fablabbcn/smartcitizen-kit-gases-pro-board/test_utils/data/source_A_board_1/source_W_board_1_lin_06.ods

Corriente | pedida | -1400 | - | corriente | leida_W | -1401.66 | 1.66 | pot0W_g | 3 | - | pot1W_f | 168
Corriente | pedida | -1399 | - | corriente | leida_W | -1400.64 | 1.64 | pot0W_g | 3 | - | pot1W_f | 179
Corriente | pedida | -1398 | - | corriente | leida_W | -1399.59 | 1.59 | pot0W_g | 3 | - | pot1W_f | 190
Corriente | pedida | -1397 | - | corriente | leida_W | -1398.64 | 1.64 | pot0W_g | 3 | - | pot1W_f | 200
Corriente | pedida | -1396 | - | corriente | leida_W | -1397.77 | 1.77 | pot0W_g | 3 | - | pot1W_f | 209
Corriente | pedida | -1395 | - | corriente | leida_W | -1396.81 | 1.81 | pot0W_g | 3 | - | pot1W_f | 219
Corriente | pedida | -1394 | - | corriente | leida_W | -1395.77 | 1.77 | pot0W_g | 3 | - | pot1W_f | 230
Corriente | pedida | -1393 | - | corriente | leida_W | -1394.59 | 1.59 | pot0W_g | 3 | - | pot1W_f | 242
Corriente | pedida | -1392 | - | corriente | leida_W | -1393.44 | 1.44 | pot0W_g | 4 | - | pot1W_f | 87
Corriente | pedida | -1391 | - | corriente | leida_W | -1392.45 | 1.45 | pot0W_g | 4 | - | pot1W_f | 97
Corriente | pedida | -1390 | - | corriente | leida_W | -1391.5 | 1.5 | pot0W_g | 4 | - | pot1W_f | 107
Corriente | pedida | -1389 | - | corriente | leida_W | -1390.45 | 1.45 | pot0W_g | 4 | - | pot1W_f | 118
Corriente | pedida | -1388 | - | corriente | leida_W | -1389.52 | 1.52 | pot0W_g | 4 | - | pot1W_f | 128
Corriente | pedida | -1387 | - | corriente | leida_W | -1388.48 | 1.48 | pot0W_g | 4 | - | pot1W_f | 139
Corriente | pedida | -1386 | - | corriente | leida_W | -1387.5 | 1.5 | pot0W_g | 4 | - | pot1W_f | 149
Corriente | pedida | -1385 | - | corriente | leida_W | -1386.44 | 1.44 | pot0W_g | 4 | - | pot1W_f | 160
Corriente | pedida | -1384 | - | corriente | leida_W | -1385.48 | 1.48 | pot0W_g | 4 | - | pot1W_f | 170
Corriente | pedida | -1383 | - | corriente | leida_W | -1384.53 | 1.53 | pot0W_g | 4 | - | pot1W_f | 180
Corriente | pedida | -1382 | - | corriente | leida_W | -1383.48 | 1.48 | pot0W_g | 4 | - | pot1W_f | 191
Corriente | pedida | -1381 | - | corriente | leida_W | -1382.52 | 1.52 | pot0W_g | 4 | - | pot1W_f | 201
Corriente | pedida | -1380 | - | corriente | leida_W | -1381.47 | 1.47 | pot0W_g | 4 | - | pot1W_f | 212
Corriente | pedida | -1379 | - | corriente | leida_W | -1380.48 | 1.48 | pot0W_g | 4 | - | pot1W_f | 222
Corriente | pedida | -1378 | - | corriente | leida_W | -1379.45 | 1.45 | pot0W_g | 4 | - | pot1W_f | 233
Corriente | pedida | -1377 | - | corriente | leida_W | -1378.48 | 1.48 | pot0W_g | 4 | - | pot1W_f | 243
Corriente | pedida | -1376 | - | corriente | leida_W | -1377.48 | 1.48 | pot0W_g | 5 | - | pot1W_f | 82
Corriente | pedida | -1375 | - | corriente | leida_W | -1376.55 | 1.55 | pot0W_g | 5 | - | pot1W_f | 92
Corriente | pedida | -1374 | - | corriente | leida_W | -1375.5 | 1.5 | pot0W_g | 5 | - | pot1W_f | 103
Corriente | pedida | -1373 | - | corriente | leida_W | -1374.56 | 1.56 | pot0W_g | 5 | - | pot1W_f | 113
Corriente | pedida | -1372 | - | corriente | leida_W | -1373.48 | 1.48 | pot0W_g | 5 | - | pot1W_f | 124
Corriente | pedida | -1371 | - | corriente | leida_W | -1372.44 | 1.44 | pot0W_g | 5 | - | pot1W_f | 135
Corriente | pedida | -1370 | - | corriente | leida_W | -1371.5 | 1.5 | pot0W_g | 5 | - | pot1W_f | 145
Corriente | pedida | -1369 | - | corriente | leida_W | -1370.42 | 1.42 | pot0W_g | 5 | - | pot1W_f | 156
Corriente | pedida | -1368 | - | corriente | leida_W | -1369.5 | 1.5 | pot0W_g | 5 | - | pot1W_f | 166
Corriente | pedida | -1367 | - | corriente | leida_W | -1368.44 | 1.44 | pot0W_g | 5 | - | pot1W_f | 177
Corriente | pedida | -1366 | - | corriente | leida_W | -1367.39 | 1.39 | pot0W_g | 5 | - | pot1W_f | 188
Corriente | pedida | -1365 | - | corriente | leida_W | -1366.42 | 1.42 | pot0W_g | 5 | - | pot1W_f | 198
Corriente | pedida | -1364 | - | corriente | leida_W | -1365.45 | 1.45 | pot0W_g | 5 | - | pot1W_f | 208
Corriente | pedida | -1363 | - | corriente | leida_W | -1364.45 | 1.45 | pot0W_g | 5 | - | pot1W_f | 219
Corriente | pedida | -1362 | - | corriente | leida_W | -1363.48 | 1.48 | pot0W_g | 5 | - | pot1W_f | 229
Corriente | pedida | -1361 | - | corriente | leida_W | -1362.39 | 1.39 | pot0W_g | 5 | - | pot1W_f | 240
Corriente | pedida | -1360 | - | corriente | leida_W | -1361.39 | 1.39 | pot0W_g | 6 | - | pot1W_f | 86
Corriente | pedida | -1359 | - | corriente | leida_W | -1360.44 | 1.44 | pot0W_g | 6 | - | pot1W_f | 96
Corriente | pedida | -1358 | - | corriente | leida_W | -1359.47 | 1.47 | pot0W_g | 6 | - | pot1W_f | 106
Corriente | pedida | -1357 | - | corriente | leida_W | -1358.42 | 1.42 | pot0W_g | 6 | - | pot1W_f | 117
Corriente | pedida | -1356 | - | corriente | leida_W | -1357.38 | 1.38 | pot0W_g | 6 | - | pot1W_f | 128
Corriente | pedida | -1355 | - | corriente | leida_W | -1356.45 | 1.45 | pot0W_g | 6 | - | pot1W_f | 138
Corriente | pedida | -1354 | - | corriente | leida_W | -1355.47 | 1.47 | pot0W_g | 6 | - | pot1W_f | 148
Corriente | pedida | -1353 | - | corriente | leida_W | -1354.41 | 1.41 | pot0W_g | 6 | - | pot1W_f | 159
Corriente | pedida | -1352 | - | corriente | leida_W | -1353.44 | 1.44 | pot0W_g | 6 | - | pot1W_f | 169
Corriente | pedida | -1351 | - | corriente | leida_W | -1352.41 | 1.41 | pot0W_g | 6 | - | pot1W_f | 180
Corriente | pedida | -1350 | - | corriente | leida_W | -1351.47 | 1.47 | pot0W_g | 6 | - | pot1W_f | 190
Corriente | pedida | -1349 | - | corriente | leida_W | -1350.39 | 1.39 | pot0W_g | 6 | - | pot1W_f | 201
Corriente | pedida | -1348 | - | corriente | leida_W | -1349.45 | 1.45 | pot0W_g | 6 | - | pot1W_f | 211
Corriente | pedida | -1347 | - | corriente | leida_W | -1348.39 | 1.39 | pot0W_g | 6 | - | pot1W_f | 222
Corriente | pedida | -1346 | - | corriente | leida_W | -1347.41 | 1.41 | pot0W_g | 6 | - | pot1W_f | 232
Corriente | pedida | -1345 | - | corriente | leida_W | -1346.47 | 1.47 | pot0W_g | 6 | - | pot1W_f | 242
Corriente | pedida | -1344 | - | corriente | leida_W | -1345.38 | 1.38 | pot0W_g | 7 | - | pot1W_f | 90
Corriente | pedida | -1343 | - | corriente | leida_W | -1344.39 | 1.39 | pot0W_g | 7 | - | pot1W_f | 100
Corriente | pedida | -1342 | - | corriente | leida_W | -1343.34 | 1.34 | pot0W_g | 7 | - | pot1W_f | 111
Corriente | pedida | -1341 | - | corriente | leida_W | -1342.39 | 1.39 | pot0W_g | 7 | - | pot1W_f | 121
Corriente | pedida | -1340 | - | corriente | leida_W | -1341.34 | 1.34 | pot0W_g | 7 | - | pot1W_f | 132
Corriente | pedida | -1339 | - | corriente | leida_W | -1340.41 | 1.41 | pot0W_g | 7 | - | pot1W_f | 142
Corriente | pedida | -1338 | - | corriente | leida_W | -1339.33 | 1.33 | pot0W_g | 7 | - | pot1W_f | 153
Corriente | pedida | -1337 | - | corriente | leida_W | -1338.38 | 1.38 | pot0W_g | 7 | - | pot1W_f | 163
Corriente | pedida | -1336 | - | corriente | leida_W | -1337.33 | 1.33 | pot0W_g | 7 | - | pot1W_f | 174
Corriente | pedida | -1335 | - | corriente | leida_W | -1336.31 | 1.31 | pot0W_g | 7 | - | pot1W_f | 185
Corriente | pedida | -1334 | - | corriente | leida_W | -1335.34 | 1.34 | pot0W_g | 7 | - | pot1W_f | 195
Corriente | pedida | -1333 | - | corriente | leida_W | -1334.31 | 1.31 | pot0W_g | 7 | - | pot1W_f | 206
Corriente | pedida | -1332 | - | corriente | leida_W | -1333.33 | 1.33 | pot0W_g | 7 | - | pot1W_f | 216
Corriente | pedida | -1331 | - | corriente | leida_W | -1332.27 | 1.27 | pot0W_g | 7 | - | pot1W_f | 227
Corriente | pedida | -1330 | - | corriente | leida_W | -1331.3 | 1.3 | pot0W_g | 7 | - | pot1W_f | 237
Corriente | pedida | -1329 | - | corriente | leida_W | -1330.23 | 1.23 | pot0W_g | 7 | - | pot1W_f | 248
Corriente | pedida | -1328 | - | corriente | leida_W | -1329.3 | 1.3 | pot0W_g | 8 | - | pot1W_f | 114
Corriente | pedida | -1327 | - | corriente | leida_W | -1328.38 | 1.38 | pot0W_g | 8 | - | pot1W_f | 124
Corriente | pedida | -1326 | - | corriente | leida_W | -1327.28 | 1.28 | pot0W_g | 8 | - | pot1W_f | 135
Corriente | pedida | -1325 | - | corriente | leida_W | -1326.25 | 1.25 | pot0W_g | 8 | - | pot1W_f | 146
Corriente | pedida | -1324 | - | corriente | leida_W | -1325.3 | 1.3 | pot0W_g | 8 | - | pot1W_f | 156
Corriente | pedida | -1323 | - | corriente | leida_W | -1324.33 | 1.33 | pot0W_g | 8 | - | pot1W_f | 166
Corriente | pedida | -1322 | - | corriente | leida_W | -1323.3 | 1.3 | pot0W_g | 8 | - | pot1W_f | 177
Corriente | pedida | -1321 | - | corriente | leida_W | -1322.27 | 1.27 | pot0W_g | 8 | - | pot1W_f | 188
Corriente | pedida | -1320 | - | corriente | leida_W | -1321.3 | 1.3 | pot0W_g | 8 | - | pot1W_f | 198
Corriente | pedida | -1319 | - | corriente | leida_W | -1320.22 | 1.22 | pot0W_g | 8 | - | pot1W_f | 209
Corriente | pedida | -1318 | - | corriente | leida_W | -1319.28 | 1.28 | pot0W_g | 8 | - | pot1W_f | 219
Corriente | pedida | -1317 | - | corriente | leida_W | -1318.31 | 1.31 | pot0W_g | 8 | - | pot1W_f | 229
Corriente | pedida | -1316 | - | corriente | leida_W | -1317.25 | 1.25 | pot0W_g | 8 | - | pot1W_f | 240
Corriente | pedida | -1315 | - | corriente | leida_W | -1316.25 | 1.25 | pot0W_g | 9 | - | pot1W_f | 91
Corriente | pedida | -1314 | - | corriente | leida_W | -1315.3 | 1.3 | pot0W_g | 9 | - | pot1W_f | 101
Corriente | pedida | -1313 | - | corriente | leida_W | -1314.36 | 1.36 | pot0W_g | 9 | - | pot1W_f | 111
Corriente | pedida | -1312 | - | corriente | leida_W | -1313.3 | 1.3 | pot0W_g | 9 | - | pot1W_f | 122
Corriente | pedida | -1311 | - | corriente | leida_W | -1312.33 | 1.33 | pot0W_g | 9 | - | pot1W_f | 132
Corriente | pedida | -1310 | - | corriente | leida_W | -1311.31 | 1.31 | pot0W_g | 9 | - | pot1W_f | 143
Corriente | pedida | -1309 | - | corriente | leida_W | -1310.33 | 1.33 | pot0W_g | 9 | - | pot1W_f | 153
Corriente | pedida | -1308 | - | corriente | leida_W | -1309.28 | 1.28 | pot0W_g | 9 | - | pot1W_f | 164
Corriente | pedida | -1307 | - | corriente | leida_W | -1308.33 | 1.33 | pot0W_g | 9 | - | pot1W_f | 174
Corriente | pedida | -1306 | - | corriente | leida_W | -1307.28 | 1.28 | pot0W_g | 9 | - | pot1W_f | 185
Corriente | pedida | -1305 | - | corriente | leida_W | -1306.33 | 1.33 | pot0W_g | 9 | - | pot1W_f | 195
Corriente | pedida | -1304 | - | corriente | leida_W | -1305.27 | 1.27 | pot0W_g | 9 | - | pot1W_f | 206
Corriente | pedida | -1303 | - | corriente | leida_W | -1304.33 | 1.33 | pot0W_g | 9 | - | pot1W_f | 216
Corriente | pedida | -1302 | - | corriente | leida_W | -1303.27 | 1.27 | pot0W_g | 9 | - | pot1W_f | 227
Corriente | pedida | -1301 | - | corriente | leida_W | -1302.31 | 1.31 | pot0W_g | 9 | - | pot1W_f | 237
Corriente | pedida | -1300 | - | corriente | leida_W | -1301.33 | 1.33 | pot0W_g | 9 | - | pot1W_f | 247
Corriente | pedida | -1299 | - | corriente | leida_W | -1300.22 | 1.22 | pot0W_g | 10 | - | pot1W_f | 98
Corriente | pedida | -1298 | - | corriente | leida_W | -1299.28 | 1.28 | pot0W_g | 10 | - | pot1W_f | 108
Corriente | pedida | -1297 | - | corriente | leida_W | -1298.34 | 1.34 | pot0W_g | 10 | - | pot1W_f | 118
Corriente | pedida | -1296 | - | corriente | leida_W | -1297.3 | 1.3 | pot0W_g | 10 | - | pot1W_f | 129
Corriente | pedida | -1295 | - | corriente | leida_W | -1296.34 | 1.34 | pot0W_g | 10 | - | pot1W_f | 139
Corriente | pedida | -1294 | - | corriente | leida_W | -1295.3 | 1.3 | pot0W_g | 10 | - | pot1W_f | 150
Corriente | pedida | -1293 | - | corriente | leida_W | -1294.31 | 1.31 | pot0W_g | 10 | - | pot1W_f | 160
Corriente | pedida | -1292 | - | corriente | leida_W | -1293.28 | 1.28 | pot0W_g | 10 | - | pot1W_f | 171
Corriente | pedida | -1291 | - | corriente | leida_W | -1292.34 | 1.34 | pot0W_g | 10 | - | pot1W_f | 181
Corriente | pedida | -1290 | - | corriente | leida_W | -1291.38 | 1.38 | pot0W_g | 10 | - | pot1W_f | 191
Corriente | pedida | -1289 | - | corriente | leida_W | -1290.31 | 1.31 | pot0W_g | 10 | - | pot1W_f | 202
Corriente | pedida | -1288 | - | corriente | leida_W | -1289.38 | 1.38 | pot0W_g | 10 | - | pot1W_f | 212
Corriente | pedida | -1287 | - | corriente | leida_W | -1288.3 | 1.3 | pot0W_g | 10 | - | pot1W_f | 223
Corriente | pedida | -1286 | - | corriente | leida_W | -1287.34 | 1.34 | pot0W_g | 10 | - | pot1W_f | 233
Corriente | pedida | -1285 | - | corriente | leida_W | -1286.3 | 1.3 | pot0W_g | 10 | - | pot1W_f | 244
Corriente | pedida | -1284 | - | corriente | leida_W | -1285.25 | 1.25 | pot0W_g | 11 | - | pot1W_f | 100
Corriente | pedida | -1283 | - | corriente | leida_W | -1284.27 | 1.27 | pot0W_g | 11 | - | pot1W_f | 110
Corriente | pedida | -1282 | - | corriente | leida_W | -1283.31 | 1.31 | pot0W_g | 11 | - | pot1W_f | 120
Corriente | pedida | -1281 | - | corriente | leida_W | -1282.27 | 1.27 | pot0W_g | 11 | - | pot1W_f | 131
Corriente | pedida | -1280 | - | corriente | leida_W | -1281.33 | 1.33 | pot0W_g | 11 | - | pot1W_f | 141
Corriente | pedida | -1279 | - | corriente | leida_W | -1280.27 | 1.27 | pot0W_g | 11 | - | pot1W_f | 152
Corriente | pedida | -1278 | - | corriente | leida_W | -1279.23 | 1.23 | pot0W_g | 11 | - | pot1W_f | 163
Corriente | pedida | -1277 | - | corriente | leida_W | -1278.25 | 1.25 | pot0W_g | 11 | - | pot1W_f | 173
Corriente | pedida | -1276 | - | corriente | leida_W | -1277.19 | 1.19 | pot0W_g | 11 | - | pot1W_f | 184
Corriente | pedida | -1275 | - | corriente | leida_W | -1276.28 | 1.28 | pot0W_g | 11 | - | pot1W_f | 194
Corriente | pedida | -1274 | - | corriente | leida_W | -1275.2 | 1.2 | pot0W_g | 11 | - | pot1W_f | 205
Corriente | pedida | -1273 | - | corriente | leida_W | -1274.27 | 1.27 | pot0W_g | 11 | - | pot1W_f | 215
Corriente | pedida | -1272 | - | corriente | leida_W | -1273.19 | 1.19 | pot0W_g | 11 | - | pot1W_f | 226
Corriente | pedida | -1271 | - | corriente | leida_W | -1272.23 | 1.23 | pot0W_g | 11 | - | pot1W_f | 236
Corriente | pedida | -1270 | - | corriente | leida_W | -1271.17 | 1.17 | pot0W_g | 11 | - | pot1W_f | 247
Corriente | pedida | -1269 | - | corriente | leida_W | -1270.16 | 1.16 | pot0W_g | 12 | - | pot1W_f | 102
Corriente | pedida | -1268 | - | corriente | leida_W | -1269.2 | 1.2 | pot0W_g | 12 | - | pot1W_f | 112
Corriente | pedida | -1267 | - | corriente | leida_W | -1268.14 | 1.14 | pot0W_g | 12 | - | pot1W_f | 123
Corriente | pedida | -1266 | - | corriente | leida_W | -1267.19 | 1.19 | pot0W_g | 12 | - | pot1W_f | 133
Corriente | pedida | -1265 | - | corriente | leida_W | -1266.14 | 1.14 | pot0W_g | 12 | - | pot1W_f | 144
Corriente | pedida | -1264 | - | corriente | leida_W | -1265.17 | 1.17 | pot0W_g | 12 | - | pot1W_f | 154
Corriente | pedida | -1263 | - | corriente | leida_W | -1264.2 | 1.2 | pot0W_g | 12 | - | pot1W_f | 164
Corriente | pedida | -1262 | - | corriente | leida_W | -1263.17 | 1.17 | pot0W_g | 12 | - | pot1W_f | 175
Corriente | pedida | -1261 | - | corriente | leida_W | -1262.11 | 1.11 | pot0W_g | 12 | - | pot1W_f | 186
Corriente | pedida | -1260 | - | corriente | leida_W | -1261.14 | 1.14 | pot0W_g | 12 | - | pot1W_f | 196
Corriente | pedida | -1259 | - | corriente | leida_W | -1260.08 | 1.08 | pot0W_g | 12 | - | pot1W_f | 207
Corriente | pedida | -1258 | - | corriente | leida_W | -1259.13 | 1.13 | pot0W_g | 12 | - | pot1W_f | 217
Corriente | pedida | -1257 | - | corriente | leida_W | -1258.06 | 1.06 | pot0W_g | 12 | - | pot1W_f | 228
Corriente | pedida | -1256 | - | corriente | leida_W | -1257.11 | 1.11 | pot0W_g | 12 | - | pot1W_f | 238
Corriente | pedida | -1255 | - | corriente | leida_W | -1256.11 | 1.11 | pot0W_g | 12 | - | pot1W_f | 248
Corriente | pedida | -1254 | - | corriente | leida_W | -1255.13 | 1.13 | pot0W_g | 13 | - | pot1W_f | 99
Corriente | pedida | -1253 | - | corriente | leida_W | -1254.11 | 1.11 | pot0W_g | 13 | - | pot1W_f | 110
Corriente | pedida | -1252 | - | corriente | leida_W | -1253.14 | 1.14 | pot0W_g | 13 | - | pot1W_f | 120
Corriente | pedida | -1251 | - | corriente | leida_W | -1252.09 | 1.09 | pot0W_g | 13 | - | pot1W_f | 131
Corriente | pedida | -1250 | - | corriente | leida_W | -1251.14 | 1.14 | pot0W_g | 13 | - | pot1W_f | 141
Corriente | pedida | -1249 | - | corriente | leida_W | -1250.19 | 1.19 | pot0W_g | 13 | - | pot1W_f | 151
Corriente | pedida | -1248 | - | corriente | leida_W | -1249.13 | 1.13 | pot0W_g | 13 | - | pot1W_f | 162
Corriente | pedida | -1247 | - | corriente | leida_W | -1248.08 | 1.08 | pot0W_g | 13 | - | pot1W_f | 173
Corriente | pedida | -1246 | - | corriente | leida_W | -1247.14 | 1.14 | pot0W_g | 13 | - | pot1W_f | 183
Corriente | pedida | -1245 | - | corriente | leida_W | -1246.08 | 1.08 | pot0W_g | 13 | - | pot1W_f | 194
Corriente | pedida | -1244 | - | corriente | leida_W | -1245.13 | 1.13 | pot0W_g | 13 | - | pot1W_f | 204
Corriente | pedida | -1243 | - | corriente | leida_W | -1244.16 | 1.16 | pot0W_g | 13 | - | pot1W_f | 214
Corriente | pedida | -1242 | - | corriente | leida_W | -1243.11 | 1.11 | pot0W_g | 13 | - | pot1W_f | 225
Corriente | pedida | -1241 | - | corriente | leida_W | -1242.13 | 1.13 | pot0W_g | 13 | - | pot1W_f | 235
Corriente | pedida | -1240 | - | corriente | leida_W | -1241.08 | 1.08 | pot0W_g | 13 | - | pot1W_f | 246
Corriente | pedida | -1239 | - | corriente | leida_W | -1240.06 | 1.06 | pot0W_g | 14 | - | pot1W_f | 103
Corriente | pedida | -1238 | - | corriente | leida_W | -1239.11 | 1.11 | pot0W_g | 14 | - | pot1W_f | 113
Corriente | pedida | -1237 | - | corriente | leida_W | -1238.05 | 1.05 | pot0W_g | 14 | - | pot1W_f | 124
Corriente | pedida | -1236 | - | corriente | leida_W | -1237.11 | 1.11 | pot0W_g | 14 | - | pot1W_f | 134
Corriente | pedida | -1235 | - | corriente | leida_W | -1236.05 | 1.05 | pot0W_g | 14 | - | pot1W_f | 145
Corriente | pedida | -1234 | - | corriente | leida_W | -1235.09 | 1.09 | pot0W_g | 14 | - | pot1W_f | 155
Corriente | pedida | -1233 | - | corriente | leida_W | -1234.14 | 1.14 | pot0W_g | 14 | - | pot1W_f | 165
Corriente | pedida | -1232 | - | corriente | leida_W | -1233.09 | 1.09 | pot0W_g | 14 | - | pot1W_f | 176
Corriente | pedida | -1231 | - | corriente | leida_W | -1232.02 | 1.02 | pot0W_g | 14 | - | pot1W_f | 187
Corriente | pedida | -1230 | - | corriente | leida_W | -1231.06 | 1.06 | pot0W_g | 14 | - | pot1W_f | 197
Corriente | pedida | -1229 | - | corriente | leida_W | -1230.11 | 1.11 | pot0W_g | 14 | - | pot1W_f | 207
Corriente | pedida | -1228 | - | corriente | leida_W | -1229.06 | 1.06 | pot0W_g | 14 | - | pot1W_f | 218
Corriente | pedida | -1227 | - | corriente | leida_W | -1228.09 | 1.09 | pot0W_g | 14 | - | pot1W_f | 228
Corriente | pedida | -1226 | - | corriente | leida_W | -1227.06 | 1.06 | pot0W_g | 14 | - | pot1W_f | 239
Corriente | pedida | -1225 | - | corriente | leida_W | -1226.09 | 1.09 | pot0W_g | 14 | - | pot1W_f | 249
Corriente | pedida | -1224 | - | corriente | leida_W | -1225.09 | 1.09 | pot0W_g | 15 | - | pot1W_f | 107
Corriente | pedida | -1223 | - | corriente | leida_W | -1224.13 | 1.13 | pot0W_g | 15 | - | pot1W_f | 117
Corriente | pedida | -1222 | - | corriente | leida_W | -1223.08 | 1.08 | pot0W_g | 15 | - | pot1W_f | 128
Corriente | pedida | -1221 | - | corriente | leida_W | -1222.11 | 1.11 | pot0W_g | 15 | - | pot1W_f | 138
Corriente | pedida | -1220 | - | corriente | leida_W | -1221.09 | 1.09 | pot0W_g | 15 | - | pot1W_f | 149
Corriente | pedida | -1219 | - | corriente | leida_W | -1220.02 | 1.02 | pot0W_g | 15 | - | pot1W_f | 160
Corriente | pedida | -1218 | - | corriente | leida_W | -1219.09 | 1.09 | pot0W_g | 15 | - | pot1W_f | 170
Corriente | pedida | -1217 | - | corriente | leida_W | -1218.13 | 1.13 | pot0W_g | 15 | - | pot1W_f | 180
Corriente | pedida | -1216 | - | corriente | leida_W | -1217.06 | 1.06 | pot0W_g | 15 | - | pot1W_f | 191
Corriente | pedida | -1215 | - | corriente | leida_W | -1216.13 | 1.13 | pot0W_g | 15 | - | pot1W_f | 201
Corriente | pedida | -1214 | - | corriente | leida_W | -1215.06 | 1.06 | pot0W_g | 15 | - | pot1W_f | 212
Corriente | pedida | -1213 | - | corriente | leida_W | -1214.13 | 1.13 | pot0W_g | 15 | - | pot1W_f | 222
Corriente | pedida | -1212 | - | corriente | leida_W | -1213.06 | 1.06 | pot0W_g | 15 | - | pot1W_f | 233
Corriente | pedida | -1211 | - | corriente | leida_W | -1212.09 | 1.09 | pot0W_g | 15 | - | pot1W_f | 243
Corriente | pedida | -1210 | - | corriente | leida_W | -1211.13 | 1.13 | pot0W_g | 16 | - | pot1W_f | 91
Corriente | pedida | -1209 | - | corriente | leida_W | -1210.16 | 1.16 | pot0W_g | 16 | - | pot1W_f | 101
Corriente | pedida | -1208 | - | corriente | leida_W | -1209.09 | 1.09 | pot0W_g | 16 | - | pot1W_f | 112
Corriente | pedida | -1207 | - | corriente | leida_W | -1208.14 | 1.14 | pot0W_g | 16 | - | pot1W_f | 122
Corriente | pedida | -1206 | - | corriente | leida_W | -1207.11 | 1.11 | pot0W_g | 16 | - | pot1W_f | 133
Corriente | pedida | -1205 | - | corriente | leida_W | -1206.14 | 1.14 | pot0W_g | 16 | - | pot1W_f | 143
Corriente | pedida | -1204 | - | corriente | leida_W | -1205.09 | 1.09 | pot0W_g | 16 | - | pot1W_f | 154
Corriente | pedida | -1203 | - | corriente | leida_W | -1204.16 | 1.16 | pot0W_g | 16 | - | pot1W_f | 164
Corriente | pedida | -1202 | - | corriente | leida_W | -1203.09 | 1.09 | pot0W_g | 16 | - | pot1W_f | 175
Corriente | pedida | -1201 | - | corriente | leida_W | -1202.14 | 1.14 | pot0W_g | 16 | - | pot1W_f | 185
Corriente | pedida | -1200 | - | corriente | leida_W | -1201.19 | 1.19 | pot0W_g | 16 | - | pot1W_f | 195
Corriente | pedida | -1199 | - | corriente | leida_W | -1200.14 | 1.14 | pot0W_g | 16 | - | pot1W_f | 206
Corriente | pedida | -1198 | - | corriente | leida_W | -1199.19 | 1.19 | pot0W_g | 16 | - | pot1W_f | 216
Corriente | pedida | -1197 | - | corriente | leida_W | -1198.11 | 1.11 | pot0W_g | 16 | - | pot1W_f | 227
Corriente | pedida | -1196 | - | corriente | leida_W | -1197.17 | 1.17 | pot0W_g | 16 | - | pot1W_f | 237
Corriente | pedida | -1195 | - | corriente | leida_W | -1196.19 | 1.19 | pot0W_g | 16 | - | pot1W_f | 247
Corriente | pedida | -1194 | - | corriente | leida_W | -1195.19 | 1.19 | pot0W_g | 17 | - | pot1W_f | 109
Corriente | pedida | -1193 | - | corriente | leida_W | -1194.23 | 1.23 | pot0W_g | 17 | - | pot1W_f | 119
Corriente | pedida | -1192 | - | corriente | leida_W | -1193.16 | 1.16 | pot0W_g | 17 | - | pot1W_f | 130
Corriente | pedida | -1191 | - | corriente | leida_W | -1192.11 | 1.11 | pot0W_g | 17 | - | pot1W_f | 141
Corriente | pedida | -1190 | - | corriente | leida_W | -1191.14 | 1.14 | pot0W_g | 17 | - | pot1W_f | 151
Corriente | pedida | -1189 | - | corriente | leida_W | -1190.17 | 1.17 | pot0W_g | 17 | - | pot1W_f | 161
Corriente | pedida | -1188 | - | corriente | leida_W | -1189.11 | 1.11 | pot0W_g | 17 | - | pot1W_f | 172
Corriente | pedida | -1187 | - | corriente | leida_W | -1188.19 | 1.19 | pot0W_g | 17 | - | pot1W_f | 182
Corriente | pedida | -1186 | - | corriente | leida_W | -1187.14 | 1.14 | pot0W_g | 17 | - | pot1W_f | 193
Corriente | pedida | -1185 | - | corriente | leida_W | -1186.16 | 1.16 | pot0W_g | 17 | - | pot1W_f | 203
Corriente | pedida | -1184 | - | corriente | leida_W | -1185.09 | 1.09 | pot0W_g | 17 | - | pot1W_f | 214
Corriente | pedida | -1183 | - | corriente | leida_W | -1184.05 | 1.05 | pot0W_g | 17 | - | pot1W_f | 225
Corriente | pedida | -1182 | - | corriente | leida_W | -1183.17 | 1.17 | pot0W_g | 17 | - | pot1W_f | 234
Corriente | pedida | -1181 | - | corriente | leida_W | -1182.11 | 1.11 | pot0W_g | 17 | - | pot1W_f | 245
Corriente | pedida | -1180 | - | corriente | leida_W | -1181.06 | 1.06 | pot0W_g | 18 | - | pot1W_f | 106
Corriente | pedida | -1179 | - | corriente | leida_W | -1180.13 | 1.13 | pot0W_g | 18 | - | pot1W_f | 116
Corriente | pedida | -1178 | - | corriente | leida_W | -1179.16 | 1.16 | pot0W_g | 18 | - | pot1W_f | 126
Corriente | pedida | -1177 | - | corriente | leida_W | -1178.13 | 1.13 | pot0W_g | 18 | - | pot1W_f | 137
Corriente | pedida | -1176 | - | corriente | leida_W | -1177.08 | 1.08 | pot0W_g | 18 | - | pot1W_f | 148
Corriente | pedida | -1175 | - | corriente | leida_W | -1176.11 | 1.11 | pot0W_g | 18 | - | pot1W_f | 158
Corriente | pedida | -1174 | - | corriente | leida_W | -1175.16 | 1.16 | pot0W_g | 18 | - | pot1W_f | 168
Corriente | pedida | -1173 | - | corriente | leida_W | -1174.13 | 1.13 | pot0W_g | 18 | - | pot1W_f | 179
Corriente | pedida | -1172 | - | corriente | leida_W | -1173.17 | 1.17 | pot0W_g | 18 | - | pot1W_f | 189
Corriente | pedida | -1171 | - | corriente | leida_W | -1172.14 | 1.14 | pot0W_g | 18 | - | pot1W_f | 200
Corriente | pedida | -1170 | - | corriente | leida_W | -1171.14 | 1.14 | pot0W_g | 18 | - | pot1W_f | 210
Corriente | pedida | -1169 | - | corriente | leida_W | -1170.11 | 1.11 | pot0W_g | 18 | - | pot1W_f | 221
Corriente | pedida | -1168 | - | corriente | leida_W | -1169.14 | 1.14 | pot0W_g | 18 | - | pot1W_f | 231
Corriente | pedida | -1167 | - | corriente | leida_W | -1168.17 | 1.17 | pot0W_g | 18 | - | pot1W_f | 241
Corriente | pedida | -1166 | - | corriente | leida_W | -1167.06 | 1.06 | pot0W_g | 19 | - | pot1W_f | 108
Corriente | pedida | -1165 | - | corriente | leida_W | -1166.11 | 1.11 | pot0W_g | 19 | - | pot1W_f | 118
Corriente | pedida | -1164 | - | corriente | leida_W | -1165.13 | 1.13 | pot0W_g | 19 | - | pot1W_f | 128
Corriente | pedida | -1163 | - | corriente | leida_W | -1164.09 | 1.09 | pot0W_g | 19 | - | pot1W_f | 139
Corriente | pedida | -1162 | - | corriente | leida_W | -1163.13 | 1.13 | pot0W_g | 19 | - | pot1W_f | 149
Corriente | pedida | -1161 | - | corriente | leida_W | -1162.08 | 1.08 | pot0W_g | 19 | - | pot1W_f | 160
Corriente | pedida | -1160 | - | corriente | leida_W | -1161.13 | 1.13 | pot0W_g | 19 | - | pot1W_f | 170
Corriente | pedida | -1159 | - | corriente | leida_W | -1160.17 | 1.17 | pot0W_g | 19 | - | pot1W_f | 180
Corriente | pedida | -1158 | - | corriente | leida_W | -1159.14 | 1.14 | pot0W_g | 19 | - | pot1W_f | 191
Corriente | pedida | -1157 | - | corriente | leida_W | -1158.17 | 1.17 | pot0W_g | 19 | - | pot1W_f | 201
Corriente | pedida | -1156 | - | corriente | leida_W | -1157.16 | 1.16 | pot0W_g | 19 | - | pot1W_f | 212
Corriente | pedida | -1155 | - | corriente | leida_W | -1156.19 | 1.19 | pot0W_g | 19 | - | pot1W_f | 222
Corriente | pedida | -1154 | - | corriente | leida_W | -1155.22 | 1.22 | pot0W_g | 19 | - | pot1W_f | 232
Corriente | pedida | -1153 | - | corriente | leida_W | -1154.14 | 1.14 | pot0W_g | 19 | - | pot1W_f | 243
Corriente | pedida | -1152 | - | corriente | leida_W | -1153.06 | 1.06 | pot0W_g | 20 | - | pot1W_f | 109
Corriente | pedida | -1151 | - | corriente | leida_W | -1152.13 | 1.13 | pot0W_g | 20 | - | pot1W_f | 119
Corriente | pedida | -1150 | - | corriente | leida_W | -1151.16 | 1.16 | pot0W_g | 20 | - | pot1W_f | 129
Corriente | pedida | -1149 | - | corriente | leida_W | -1150.11 | 1.11 | pot0W_g | 20 | - | pot1W_f | 140
Corriente | pedida | -1148 | - | corriente | leida_W | -1149.16 | 1.16 | pot0W_g | 20 | - | pot1W_f | 150
Corriente | pedida | -1147 | - | corriente | leida_W | -1148.19 | 1.19 | pot0W_g | 20 | - | pot1W_f | 160
Corriente | pedida | -1146 | - | corriente | leida_W | -1147.23 | 1.23 | pot0W_g | 20 | - | pot1W_f | 170
Corriente | pedida | -1145 | - | corriente | leida_W | -1146.17 | 1.17 | pot0W_g | 20 | - | pot1W_f | 181
Corriente | pedida | -1144 | - | corriente | leida_W | -1145.14 | 1.14 | pot0W_g | 20 | - | pot1W_f | 192
Corriente | pedida | -1143 | - | corriente | leida_W | -1144.3 | 1.3 | pot0W_g | 20 | - | pot1W_f | 201
Corriente | pedida | -1142 | - | corriente | leida_W | -1143.22 | 1.22 | pot0W_g | 20 | - | pot1W_f | 212
Corriente | pedida | -1141 | - | corriente | leida_W | -1142.28 | 1.28 | pot0W_g | 20 | - | pot1W_f | 222
Corriente | pedida | -1140 | - | corriente | leida_W | -1141.22 | 1.22 | pot0W_g | 20 | - | pot1W_f | 233
Corriente | pedida | -1139 | - | corriente | leida_W | -1140.23 | 1.23 | pot0W_g | 20 | - | pot1W_f | 243
Corriente | pedida | -1138 | - | corriente | leida_W | -1139.19 | 1.19 | pot0W_g | 21 | - | pot1W_f | 105
Corriente | pedida | -1137 | - | corriente | leida_W | -1138.23 | 1.23 | pot0W_g | 21 | - | pot1W_f | 115
Corriente | pedida | -1136 | - | corriente | leida_W | -1137.28 | 1.28 | pot0W_g | 21 | - | pot1W_f | 125
Corriente | pedida | -1135 | - | corriente | leida_W | -1136.22 | 1.22 | pot0W_g | 21 | - | pot1W_f | 136
Corriente | pedida | -1134 | - | corriente | leida_W | -1135.27 | 1.27 | pot0W_g | 21 | - | pot1W_f | 146
Corriente | pedida | -1133 | - | corriente | leida_W | -1134.22 | 1.22 | pot0W_g | 21 | - | pot1W_f | 157
Corriente | pedida | -1132 | - | corriente | leida_W | -1133.27 | 1.27 | pot0W_g | 21 | - | pot1W_f | 167
Corriente | pedida | -1131 | - | corriente | leida_W | -1132.33 | 1.33 | pot0W_g | 21 | - | pot1W_f | 177
Corriente | pedida | -1130 | - | corriente | leida_W | -1131.27 | 1.27 | pot0W_g | 21 | - | pot1W_f | 188
Corriente | pedida | -1129 | - | corriente | leida_W | -1130.3 | 1.3 | pot0W_g | 21 | - | pot1W_f | 198
Corriente | pedida | -1128 | - | corriente | leida_W | -1129.27 | 1.27 | pot0W_g | 21 | - | pot1W_f | 209
Corriente | pedida | -1127 | - | corriente | leida_W | -1128.3 | 1.3 | pot0W_g | 21 | - | pot1W_f | 219
Corriente | pedida | -1126 | - | corriente | leida_W | -1127.34 | 1.34 | pot0W_g | 21 | - | pot1W_f | 229
Corriente | pedida | -1125 | - | corriente | leida_W | -1126.27 | 1.27 | pot0W_g | 21 | - | pot1W_f | 240
Corriente | pedida | -1124 | - | corriente | leida_W | -1125.25 | 1.25 | pot0W_g | 22 | - | pot1W_f | 107
Corriente | pedida | -1123 | - | corriente | leida_W | -1124.28 | 1.28 | pot0W_g | 22 | - | pot1W_f | 117
Corriente | pedida | -1122 | - | corriente | leida_W | -1123.34 | 1.34 | pot0W_g | 22 | - | pot1W_f | 127
Corriente | pedida | -1121 | - | corriente | leida_W | -1122.31 | 1.31 | pot0W_g | 22 | - | pot1W_f | 138
Corriente | pedida | -1120 | - | corriente | leida_W | -1121.34 | 1.34 | pot0W_g | 22 | - | pot1W_f | 148
Corriente | pedida | -1119 | - | corriente | leida_W | -1120.38 | 1.38 | pot0W_g | 22 | - | pot1W_f | 158
Corriente | pedida | -1118 | - | corriente | leida_W | -1119.36 | 1.36 | pot0W_g | 22 | - | pot1W_f | 169
Corriente | pedida | -1117 | - | corriente | leida_W | -1118.38 | 1.38 | pot0W_g | 22 | - | pot1W_f | 179
Corriente | pedida | -1116 | - | corriente | leida_W | -1117.36 | 1.36 | pot0W_g | 22 | - | pot1W_f | 190
Corriente | pedida | -1115 | - | corriente | leida_W | -1116.38 | 1.38 | pot0W_g | 22 | - | pot1W_f | 200
Corriente | pedida | -1114 | - | corriente | leida_W | -1115.33 | 1.33 | pot0W_g | 22 | - | pot1W_f | 211
Corriente | pedida | -1113 | - | corriente | leida_W | -1114.36 | 1.36 | pot0W_g | 22 | - | pot1W_f | 221
Corriente | pedida | -1112 | - | corriente | leida_W | -1113.41 | 1.41 | pot0W_g | 22 | - | pot1W_f | 231
Corriente | pedida | -1111 | - | corriente | leida_W | -1112.36 | 1.36 | pot0W_g | 22 | - | pot1W_f | 242
Corriente | pedida | -1110 | - | corriente | leida_W | -1111.39 | 1.39 | pot0W_g | 23 | - | pot1W_f | 109
Corriente | pedida | -1109 | - | corriente | leida_W | -1110.45 | 1.45 | pot0W_g | 23 | - | pot1W_f | 119
Corriente | pedida | -1108 | - | corriente | leida_W | -1109.39 | 1.39 | pot0W_g | 23 | - | pot1W_f | 130
Corriente | pedida | -1107 | - | corriente | leida_W | -1108.44 | 1.44 | pot0W_g | 23 | - | pot1W_f | 140
Corriente | pedida | -1106 | - | corriente | leida_W | -1107.39 | 1.39 | pot0W_g | 23 | - | pot1W_f | 151
Corriente | pedida | -1105 | - | corriente | leida_W | -1106.44 | 1.44 | pot0W_g | 23 | - | pot1W_f | 161
Corriente | pedida | -1104 | - | corriente | leida_W | -1105.47 | 1.47 | pot0W_g | 23 | - | pot1W_f | 171
Corriente | pedida | -1103 | - | corriente | leida_W | -1104.42 | 1.42 | pot0W_g | 23 | - | pot1W_f | 182
Corriente | pedida | -1102 | - | corriente | leida_W | -1103.38 | 1.38 | pot0W_g | 23 | - | pot1W_f | 193
Corriente | pedida | -1101 | - | corriente | leida_W | -1102.44 | 1.44 | pot0W_g | 23 | - | pot1W_f | 203
Corriente | pedida | -1100 | - | corriente | leida_W | -1101.45 | 1.45 | pot0W_g | 23 | - | pot1W_f | 213
Corriente | pedida | -1099 | - | corriente | leida_W | -1100.41 | 1.41 | pot0W_g | 23 | - | pot1W_f | 224
Corriente | pedida | -1098 | - | corriente | leida_W | -1099.44 | 1.44 | pot0W_g | 23 | - | pot1W_f | 234
Corriente | pedida | -1097 | - | corriente | leida_W | -1098.48 | 1.48 | pot0W_g | 23 | - | pot1W_f | 244
Corriente | pedida | -1096 | - | corriente | leida_W | -1097.42 | 1.42 | pot0W_g | 24 | - | pot1W_f | 104
Corriente | pedida | -1095 | - | corriente | leida_W | -1096.45 | 1.45 | pot0W_g | 24 | - | pot1W_f | 114
Corriente | pedida | -1094 | - | corriente | leida_W | -1095.42 | 1.42 | pot0W_g | 24 | - | pot1W_f | 125
Corriente | pedida | -1093 | - | corriente | leida_W | -1094.45 | 1.45 | pot0W_g | 24 | - | pot1W_f | 135
Corriente | pedida | -1092 | - | corriente | leida_W | -1093.52 | 1.52 | pot0W_g | 24 | - | pot1W_f | 145
Corriente | pedida | -1091 | - | corriente | leida_W | -1092.48 | 1.48 | pot0W_g | 24 | - | pot1W_f | 156
Corriente | pedida | -1090 | - | corriente | leida_W | -1091.52 | 1.52 | pot0W_g | 24 | - | pot1W_f | 166
Corriente | pedida | -1089 | - | corriente | leida_W | -1090.44 | 1.44 | pot0W_g | 24 | - | pot1W_f | 177
Corriente | pedida | -1088 | - | corriente | leida_W | -1089.5 | 1.5 | pot0W_g | 24 | - | pot1W_f | 187
Corriente | pedida | -1087 | - | corriente | leida_W | -1088.56 | 1.56 | pot0W_g | 24 | - | pot1W_f | 197
Corriente | pedida | -1086 | - | corriente | leida_W | -1087.52 | 1.52 | pot0W_g | 24 | - | pot1W_f | 208
Corriente | pedida | -1085 | - | corriente | leida_W | -1086.55 | 1.55 | pot0W_g | 24 | - | pot1W_f | 218
Corriente | pedida | -1084 | - | corriente | leida_W | -1085.58 | 1.58 | pot0W_g | 24 | - | pot1W_f | 228
Corriente | pedida | -1083 | - | corriente | leida_W | -1084.55 | 1.55 | pot0W_g | 24 | - | pot1W_f | 239
Corriente | pedida | -1082 | - | corriente | leida_W | -1083.52 | 1.52 | pot0W_g | 25 | - | pot1W_f | 110
Corriente | pedida | -1081 | - | corriente | leida_W | -1082.56 | 1.56 | pot0W_g | 25 | - | pot1W_f | 120
Corriente | pedida | -1080 | - | corriente | leida_W | -1081.63 | 1.63 | pot0W_g | 25 | - | pot1W_f | 130
Corriente | pedida | -1079 | - | corriente | leida_W | -1080.56 | 1.56 | pot0W_g | 25 | - | pot1W_f | 141
Corriente | pedida | -1078 | - | corriente | leida_W | -1079.61 | 1.61 | pot0W_g | 25 | - | pot1W_f | 151
Corriente | pedida | -1077 | - | corriente | leida_W | -1078.58 | 1.58 | pot0W_g | 25 | - | pot1W_f | 162
Corriente | pedida | -1076 | - | corriente | leida_W | -1077.61 | 1.61 | pot0W_g | 25 | - | pot1W_f | 172
Corriente | pedida | -1075 | - | corriente | leida_W | -1076.64 | 1.64 | pot0W_g | 25 | - | pot1W_f | 182
Corriente | pedida | -1074 | - | corriente | leida_W | -1075.59 | 1.59 | pot0W_g | 25 | - | pot1W_f | 193
Corriente | pedida | -1073 | - | corriente | leida_W | -1074.64 | 1.64 | pot0W_g | 25 | - | pot1W_f | 203
Corriente | pedida | -1072 | - | corriente | leida_W | -1073.59 | 1.59 | pot0W_g | 25 | - | pot1W_f | 214
Corriente | pedida | -1071 | - | corriente | leida_W | -1072.61 | 1.61 | pot0W_g | 25 | - | pot1W_f | 224
Corriente | pedida | -1070 | - | corriente | leida_W | -1071.56 | 1.56 | pot0W_g | 25 | - | pot1W_f | 235
Corriente | pedida | -1069 | - | corriente | leida_W | -1070.61 | 1.61 | pot0W_g | 25 | - | pot1W_f | 245
Corriente | pedida | -1068 | - | corriente | leida_W | -1069.59 | 1.59 | pot0W_g | 26 | - | pot1W_f | 115
Corriente | pedida | -1067 | - | corriente | leida_W | -1068.53 | 1.53 | pot0W_g | 26 | - | pot1W_f | 126
Corriente | pedida | -1066 | - | corriente | leida_W | -1067.59 | 1.59 | pot0W_g | 26 | - | pot1W_f | 136
Corriente | pedida | -1065 | - | corriente | leida_W | -1066.55 | 1.55 | pot0W_g | 26 | - | pot1W_f | 147
Corriente | pedida | -1064 | - | corriente | leida_W | -1065.56 | 1.56 | pot0W_g | 26 | - | pot1W_f | 157
Corriente | pedida | -1063 | - | corriente | leida_W | -1064.52 | 1.52 | pot0W_g | 26 | - | pot1W_f | 168
Corriente | pedida | -1062 | - | corriente | leida_W | -1063.58 | 1.58 | pot0W_g | 26 | - | pot1W_f | 178
Corriente | pedida | -1061 | - | corriente | leida_W | -1062.53 | 1.53 | pot0W_g | 26 | - | pot1W_f | 189
Corriente | pedida | -1060 | - | corriente | leida_W | -1061.55 | 1.55 | pot0W_g | 26 | - | pot1W_f | 199
Corriente | pedida | -1059 | - | corriente | leida_W | -1060.5 | 1.5 | pot0W_g | 26 | - | pot1W_f | 210
Corriente | pedida | -1058 | - | corriente | leida_W | -1059.53 | 1.53 | pot0W_g | 26 | - | pot1W_f | 220
Corriente | pedida | -1057 | - | corriente | leida_W | -1058.48 | 1.48 | pot0W_g | 26 | - | pot1W_f | 231
Corriente | pedida | -1056 | - | corriente | leida_W | -1057.52 | 1.52 | pot0W_g | 26 | - | pot1W_f | 241
Corriente | pedida | -1055 | - | corriente | leida_W | -1056.47 | 1.47 | pot0W_g | 27 | - | pot1W_f | 116
Corriente | pedida | -1054 | - | corriente | leida_W | -1055.41 | 1.41 | pot0W_g | 27 | - | pot1W_f | 127
Corriente | pedida | -1053 | - | corriente | leida_W | -1054.45 | 1.45 | pot0W_g | 27 | - | pot1W_f | 137
Corriente | pedida | -1052 | - | corriente | leida_W | -1053.42 | 1.42 | pot0W_g | 27 | - | pot1W_f | 148
Corriente | pedida | -1051 | - | corriente | leida_W | -1052.45 | 1.45 | pot0W_g | 27 | - | pot1W_f | 158
Corriente | pedida | -1050 | - | corriente | leida_W | -1051.39 | 1.39 | pot0W_g | 27 | - | pot1W_f | 169
Corriente | pedida | -1049 | - | corriente | leida_W | -1050.45 | 1.45 | pot0W_g | 27 | - | pot1W_f | 179
Corriente | pedida | -1048 | - | corriente | leida_W | -1049.38 | 1.38 | pot0W_g | 27 | - | pot1W_f | 190
Corriente | pedida | -1047 | - | corriente | leida_W | -1048.34 | 1.34 | pot0W_g | 27 | - | pot1W_f | 201
Corriente | pedida | -1046 | - | corriente | leida_W | -1047.39 | 1.39 | pot0W_g | 27 | - | pot1W_f | 211
Corriente | pedida | -1045 | - | corriente | leida_W | -1046.44 | 1.44 | pot0W_g | 27 | - | pot1W_f | 221
Corriente | pedida | -1044 | - | corriente | leida_W | -1045.39 | 1.39 | pot0W_g | 27 | - | pot1W_f | 232
Corriente | pedida | -1043 | - | corriente | leida_W | -1044.31 | 1.31 | pot0W_g | 27 | - | pot1W_f | 243
Corriente | pedida | -1042 | - | corriente | leida_W | -1043.28 | 1.28 | pot0W_g | 28 | - | pot1W_f | 117
Corriente | pedida | -1041 | - | corriente | leida_W | -1042.36 | 1.36 | pot0W_g | 28 | - | pot1W_f | 127
Corriente | pedida | -1040 | - | corriente | leida_W | -1041.38 | 1.38 | pot0W_g | 28 | - | pot1W_f | 137
Corriente | pedida | -1039 | - | corriente | leida_W | -1040.33 | 1.33 | pot0W_g | 28 | - | pot1W_f | 148
Corriente | pedida | -1038 | - | corriente | leida_W | -1039.38 | 1.38 | pot0W_g | 28 | - | pot1W_f | 158
Corriente | pedida | -1037 | - | corriente | leida_W | -1038.33 | 1.33 | pot0W_g | 28 | - | pot1W_f | 169
Corriente | pedida | -1036 | - | corriente | leida_W | -1037.36 | 1.36 | pot0W_g | 28 | - | pot1W_f | 179
Corriente | pedida | -1035 | - | corriente | leida_W | -1036.31 | 1.31 | pot0W_g | 28 | - | pot1W_f | 190
Corriente | pedida | -1034 | - | corriente | leida_W | -1035.38 | 1.38 | pot0W_g | 28 | - | pot1W_f | 200
Corriente | pedida | -1033 | - | corriente | leida_W | -1034.31 | 1.31 | pot0W_g | 28 | - | pot1W_f | 211
Corriente | pedida | -1032 | - | corriente | leida_W | -1033.38 | 1.38 | pot0W_g | 28 | - | pot1W_f | 221
Corriente | pedida | -1031 | - | corriente | leida_W | -1032.3 | 1.3 | pot0W_g | 28 | - | pot1W_f | 232
Corriente | pedida | -1030 | - | corriente | leida_W | -1031.31 | 1.31 | pot0W_g | 28 | - | pot1W_f | 242
Corriente | pedida | -1029 | - | corriente | leida_W | -1030.25 | 1.25 | pot0W_g | 29 | - | pot1W_f | 113
Corriente | pedida | -1028 | - | corriente | leida_W | -1029.3 | 1.3 | pot0W_g | 29 | - | pot1W_f | 123
Corriente | pedida | -1027 | - | corriente | leida_W | -1028.36 | 1.36 | pot0W_g | 29 | - | pot1W_f | 133
Corriente | pedida | -1026 | - | corriente | leida_W | -1027.3 | 1.3 | pot0W_g | 29 | - | pot1W_f | 144
Corriente | pedida | -1025 | - | corriente | leida_W | -1026.25 | 1.25 | pot0W_g | 29 | - | pot1W_f | 155
Corriente | pedida | -1024 | - | corriente | leida_W | -1025.31 | 1.31 | pot0W_g | 29 | - | pot1W_f | 165
Corriente | pedida | -1023 | - | corriente | leida_W | -1024.34 | 1.34 | pot0W_g | 29 | - | pot1W_f | 175
Corriente | pedida | -1022 | - | corriente | leida_W | -1023.31 | 1.31 | pot0W_g | 29 | - | pot1W_f | 186
Corriente | pedida | -1021 | - | corriente | leida_W | -1022.27 | 1.27 | pot0W_g | 29 | - | pot1W_f | 197
Corriente | pedida | -1020 | - | corriente | leida_W | -1021.3 | 1.3 | pot0W_g | 29 | - | pot1W_f | 207
Corriente | pedida | -1019 | - | corriente | leida_W | -1020.23 | 1.23 | pot0W_g | 29 | - | pot1W_f | 218
Corriente | pedida | -1018 | - | corriente | leida_W | -1019.25 | 1.25 | pot0W_g | 29 | - | pot1W_f | 228
Corriente | pedida | -1017 | - | corriente | leida_W | -1018.19 | 1.19 | pot0W_g | 29 | - | pot1W_f | 239
Corriente | pedida | -1016 | - | corriente | leida_W | -1017.23 | 1.23 | pot0W_g | 29 | - | pot1W_f | 249
Corriente | pedida | -1015 | - | corriente | leida_W | -1016.17 | 1.17 | pot0W_g | 30 | - | pot1W_f | 125
Corriente | pedida | -1014 | - | corriente | leida_W | -1015.22 | 1.22 | pot0W_g | 30 | - | pot1W_f | 135
Corriente | pedida | -1013 | - | corriente | leida_W | -1014.17 | 1.17 | pot0W_g | 30 | - | pot1W_f | 146
Corriente | pedida | -1012 | - | corriente | leida_W | -1013.2 | 1.2 | pot0W_g | 30 | - | pot1W_f | 156
Corriente | pedida | -1011 | - | corriente | leida_W | -1012.12 | 1.12 | pot0W_g | 30 | - | pot1W_f | 167
Corriente | pedida | -1010 | - | corriente | leida_W | -1011.19 | 1.19 | pot0W_g | 30 | - | pot1W_f | 177
Corriente | pedida | -1009 | - | corriente | leida_W | -1010.12 | 1.12 | pot0W_g | 30 | - | pot1W_f | 188
Corriente | pedida | -1008 | - | corriente | leida_W | -1009.19 | 1.19 | pot0W_g | 30 | - | pot1W_f | 198
Corriente | pedida | -1007 | - | corriente | leida_W | -1008.14 | 1.14 | pot0W_g | 30 | - | pot1W_f | 209
Corriente | pedida | -1006 | - | corriente | leida_W | -1007.17 | 1.17 | pot0W_g | 30 | - | pot1W_f | 219
Corriente | pedida | -1005 | - | corriente | leida_W | -1006.2 | 1.2 | pot0W_g | 30 | - | pot1W_f | 229
Corriente | pedida | -1004 | - | corriente | leida_W | -1005.16 | 1.16 | pot0W_g | 30 | - | pot1W_f | 240
Corriente | pedida | -1003 | - | corriente | leida_W | -1004.14 | 1.14 | pot0W_g | 31 | - | pot1W_f | 116
Corriente | pedida | -1002 | - | corriente | leida_W | -1003.19 | 1.19 | pot0W_g | 31 | - | pot1W_f | 126
Corriente | pedida | -1001 | - | corriente | leida_W | -1002.11 | 1.11 | pot0W_g | 31 | - | pot1W_f | 137
Corriente | pedida | -1000 | - | corriente | leida_W | -1001.19 | 1.19 | pot0W_g | 31 | - | pot1W_f | 147
Corriente | pedida | -999 | - | corriente | leida_W | -1000.22 | 1.22 | pot0W_g | 31 | - | pot1W_f | 157
Corriente | pedida | -998 | - | corriente | leida_W | -999.17 | 1.17 | pot0W_g | 31 | - | pot1W_f | 168
Corriente | pedida | -997 | - | corriente | leida_W | -998.2 | 1.2 | pot0W_g | 31 | - | pot1W_f | 178
Corriente | pedida | -996 | - | corriente | leida_W | -997.17 | 1.17 | pot0W_g | 31 | - | pot1W_f | 189
Corriente | pedida | -995 | - | corriente | leida_W | -996.2 | 1.2 | pot0W_g | 31 | - | pot1W_f | 199
Corriente | pedida | -994 | - | corriente | leida_W | -995.17 | 1.17 | pot0W_g | 31 | - | pot1W_f | 210
Corriente | pedida | -993 | - | corriente | leida_W | -994.19 | 1.19 | pot0W_g | 31 | - | pot1W_f | 220
Corriente | pedida | -992 | - | corriente | leida_W | -993.22 | 1.22 | pot0W_g | 31 | - | pot1W_f | 230
Corriente | pedida | -991 | - | corriente | leida_W | -992.19 | 1.19 | pot0W_g | 31 | - | pot1W_f | 241
Corriente | pedida | -990 | - | corriente | leida_W | -991.12 | 1.12 | pot0W_g | 32 | - | pot1W_f | 111
Corriente | pedida | -989 | - | corriente | leida_W | -990.17 | 1.17 | pot0W_g | 32 | - | pot1W_f | 121
Corriente | pedida | -988 | - | corriente | leida_W | -989.12 | 1.12 | pot0W_g | 32 | - | pot1W_f | 132
Corriente | pedida | -987 | - | corriente | leida_W | -988.17 | 1.17 | pot0W_g | 32 | - | pot1W_f | 142
Corriente | pedida | -986 | - | corriente | leida_W | -987.2 | 1.2 | pot0W_g | 32 | - | pot1W_f | 152
Corriente | pedida | -985 | - | corriente | leida_W | -986.16 | 1.16 | pot0W_g | 32 | - | pot1W_f | 163
Corriente | pedida | -984 | - | corriente | leida_W | -985.12 | 1.12 | pot0W_g | 32 | - | pot1W_f | 174
Corriente | pedida | -983 | - | corriente | leida_W | -984.16 | 1.16 | pot0W_g | 32 | - | pot1W_f | 184
Corriente | pedida | -982 | - | corriente | leida_W | -983.11 | 1.11 | pot0W_g | 32 | - | pot1W_f | 195
Corriente | pedida | -981 | - | corriente | leida_W | -982.14 | 1.14 | pot0W_g | 32 | - | pot1W_f | 205
Corriente | pedida | -980 | - | corriente | leida_W | -981.19 | 1.19 | pot0W_g | 32 | - | pot1W_f | 215
Corriente | pedida | -979 | - | corriente | leida_W | -980.16 | 1.16 | pot0W_g | 32 | - | pot1W_f | 226
Corriente | pedida | -978 | - | corriente | leida_W | -979.16 | 1.16 | pot0W_g | 32 | - | pot1W_f | 236
Corriente | pedida | -977 | - | corriente | leida_W | -978.11 | 1.11 | pot0W_g | 32 | - | pot1W_f | 247
Corriente | pedida | -976 | - | corriente | leida_W | -976.98 | 0.98 | pot0W_g | 33 | - | pot1W_f | 127
Corriente | pedida | -975 | - | corriente | leida_W | -976.06 | 1.06 | pot0W_g | 33 | - | pot1W_f | 137
Corriente | pedida | -974 | - | corriente | leida_W | -975.09 | 1.09 | pot0W_g | 33 | - | pot1W_f | 147
Corriente | pedida | -973 | - | corriente | leida_W | -974.02 | 1.02 | pot0W_g | 33 | - | pot1W_f | 158
Corriente | pedida | -972 | - | corriente | leida_W | -973.06 | 1.06 | pot0W_g | 33 | - | pot1W_f | 168
Corriente | pedida | -971 | - | corriente | leida_W | -972.14 | 1.14 | pot0W_g | 33 | - | pot1W_f | 178
Corriente | pedida | -970 | - | corriente | leida_W | -971.08 | 1.08 | pot0W_g | 33 | - | pot1W_f | 189
Corriente | pedida | -969 | - | corriente | leida_W | -970.02 | 1.02 | pot0W_g | 33 | - | pot1W_f | 200
Corriente | pedida | -968 | - | corriente | leida_W | -968.95 | 0.95 | pot0W_g | 33 | - | pot1W_f | 211
Corriente | pedida | -967 | - | corriente | leida_W | -968.02 | 1.02 | pot0W_g | 33 | - | pot1W_f | 221
Corriente | pedida | -966 | - | corriente | leida_W | -967.03 | 1.03 | pot0W_g | 33 | - | pot1W_f | 231
Corriente | pedida | -965 | - | corriente | leida_W | -965.97 | 0.97 | pot0W_g | 33 | - | pot1W_f | 242
Corriente | pedida | -964 | - | corriente | leida_W | -964.95 | 0.95 | pot0W_g | 34 | - | pot1W_f | 120
Corriente | pedida | -963 | - | corriente | leida_W | -964 | 1 | pot0W_g | 34 | - | pot1W_f | 130
Corriente | pedida | -962 | - | corriente | leida_W | -963.05 | 1.05 | pot0W_g | 34 | - | pot1W_f | 140
Corriente | pedida | -961 | - | corriente | leida_W | -962.09 | 1.09 | pot0W_g | 34 | - | pot1W_f | 150
Corriente | pedida | -960 | - | corriente | leida_W | -961.12 | 1.12 | pot0W_g | 34 | - | pot1W_f | 160
Corriente | pedida | -959 | - | corriente | leida_W | -960.09 | 1.09 | pot0W_g | 34 | - | pot1W_f | 171
Corriente | pedida | -958 | - | corriente | leida_W | -959.14 | 1.14 | pot0W_g | 34 | - | pot1W_f | 181
Corriente | pedida | -957 | - | corriente | leida_W | -958.09 | 1.09 | pot0W_g | 34 | - | pot1W_f | 192
Corriente | pedida | -956 | - | corriente | leida_W | -957.14 | 1.14 | pot0W_g | 34 | - | pot1W_f | 202
Corriente | pedida | -955 | - | corriente | leida_W | -956.16 | 1.16 | pot0W_g | 34 | - | pot1W_f | 212
Corriente | pedida | -954 | - | corriente | leida_W | -955.12 | 1.12 | pot0W_g | 34 | - | pot1W_f | 223
Corriente | pedida | -953 | - | corriente | leida_W | -954.16 | 1.16 | pot0W_g | 34 | - | pot1W_f | 233
Corriente | pedida | -952 | - | corriente | leida_W | -953.19 | 1.19 | pot0W_g | 34 | - | pot1W_f | 243
Corriente | pedida | -951 | - | corriente | leida_W | -952.08 | 1.08 | pot0W_g | 35 | - | pot1W_f | 126
Corriente | pedida | -950 | - | corriente | leida_W | -951.12 | 1.12 | pot0W_g | 35 | - | pot1W_f | 136
Corriente | pedida | -949 | - | corriente | leida_W | -950.08 | 1.08 | pot0W_g | 35 | - | pot1W_f | 147
Corriente | pedida | -948 | - | corriente | leida_W | -949.12 | 1.12 | pot0W_g | 35 | - | pot1W_f | 157
Corriente | pedida | -947 | - | corriente | leida_W | -948.08 | 1.08 | pot0W_g | 35 | - | pot1W_f | 168
Corriente | pedida | -946 | - | corriente | leida_W | -947.03 | 1.03 | pot0W_g | 35 | - | pot1W_f | 179
Corriente | pedida | -945 | - | corriente | leida_W | -946.08 | 1.08 | pot0W_g | 35 | - | pot1W_f | 189
Corriente | pedida | -944 | - | corriente | leida_W | -945.12 | 1.12 | pot0W_g | 35 | - | pot1W_f | 199
Corriente | pedida | -943 | - | corriente | leida_W | -944.06 | 1.06 | pot0W_g | 35 | - | pot1W_f | 210
Corriente | pedida | -942 | - | corriente | leida_W | -943.02 | 1.02 | pot0W_g | 35 | - | pot1W_f | 221
Corriente | pedida | -941 | - | corriente | leida_W | -942.05 | 1.05 | pot0W_g | 35 | - | pot1W_f | 231
Corriente | pedida | -940 | - | corriente | leida_W | -941.06 | 1.06 | pot0W_g | 35 | - | pot1W_f | 241
Corriente | pedida | -939 | - | corriente | leida_W | -940 | 1 | pot0W_g | 36 | - | pot1W_f | 123
Corriente | pedida | -938 | - | corriente | leida_W | -939.06 | 1.06 | pot0W_g | 36 | - | pot1W_f | 133
Corriente | pedida | -937 | - | corriente | leida_W | -937.98 | 0.98 | pot0W_g | 36 | - | pot1W_f | 144
Corriente | pedida | -936 | - | corriente | leida_W | -937.03 | 1.03 | pot0W_g | 36 | - | pot1W_f | 154
Corriente | pedida | -935 | - | corriente | leida_W | -936.08 | 1.08 | pot0W_g | 36 | - | pot1W_f | 164
Corriente | pedida | -934 | - | corriente | leida_W | -935.05 | 1.05 | pot0W_g | 36 | - | pot1W_f | 175
Corriente | pedida | -933 | - | corriente | leida_W | -934.09 | 1.09 | pot0W_g | 36 | - | pot1W_f | 185
Corriente | pedida | -932 | - | corriente | leida_W | -933.02 | 1.02 | pot0W_g | 36 | - | pot1W_f | 196
Corriente | pedida | -931 | - | corriente | leida_W | -931.98 | 0.98 | pot0W_g | 36 | - | pot1W_f | 207
Corriente | pedida | -930 | - | corriente | leida_W | -931.02 | 1.02 | pot0W_g | 36 | - | pot1W_f | 217
Corriente | pedida | -929 | - | corriente | leida_W | -930.05 | 1.05 | pot0W_g | 36 | - | pot1W_f | 227
Corriente | pedida | -928 | - | corriente | leida_W | -929 | 1 | pot0W_g | 36 | - | pot1W_f | 238
Corriente | pedida | -927 | - | corriente | leida_W | -928.06 | 1.06 | pot0W_g | 36 | - | pot1W_f | 248
Corriente | pedida | -926 | - | corriente | leida_W | -926.84 | 0.84 | pot0W_g | 37 | - | pot1W_f | 128
Corriente | pedida | -925 | - | corriente | leida_W | -925.98 | 0.98 | pot0W_g | 37 | - | pot1W_f | 137
Corriente | pedida | -924 | - | corriente | leida_W | -925.03 | 1.03 | pot0W_g | 37 | - | pot1W_f | 147
Corriente | pedida | -923 | - | corriente | leida_W | -924 | 1 | pot0W_g | 37 | - | pot1W_f | 158
Corriente | pedida | -922 | - | corriente | leida_W | -923.03 | 1.03 | pot0W_g | 37 | - | pot1W_f | 168
Corriente | pedida | -921 | - | corriente | leida_W | -921.97 | 0.97 | pot0W_g | 37 | - | pot1W_f | 179
Corriente | pedida | -920 | - | corriente | leida_W | -920.95 | 0.95 | pot0W_g | 37 | - | pot1W_f | 190
Corriente | pedida | -919 | - | corriente | leida_W | -920.08 | 1.08 | pot0W_g | 37 | - | pot1W_f | 199
Corriente | pedida | -918 | - | corriente | leida_W | -919.02 | 1.02 | pot0W_g | 37 | - | pot1W_f | 210
Corriente | pedida | -917 | - | corriente | leida_W | -917.97 | 0.97 | pot0W_g | 37 | - | pot1W_f | 221
Corriente | pedida | -916 | - | corriente | leida_W | -917 | 1 | pot0W_g | 37 | - | pot1W_f | 231
Corriente | pedida | -915 | - | corriente | leida_W | -915.95 | 0.95 | pot0W_g | 37 | - | pot1W_f | 242
Corriente | pedida | -914 | - | corriente | leida_W | -915.02 | 1.02 | pot0W_g | 38 | - | pot1W_f | 124
Corriente | pedida | -913 | - | corriente | leida_W | -914.05 | 1.05 | pot0W_g | 38 | - | pot1W_f | 134
Corriente | pedida | -912 | - | corriente | leida_W | -912.98 | 0.98 | pot0W_g | 38 | - | pot1W_f | 145
Corriente | pedida | -911 | - | corriente | leida_W | -912.03 | 1.03 | pot0W_g | 38 | - | pot1W_f | 155
Corriente | pedida | -910 | - | corriente | leida_W | -910.97 | 0.97 | pot0W_g | 38 | - | pot1W_f | 166
Corriente | pedida | -909 | - | corriente | leida_W | -910.02 | 1.02 | pot0W_g | 38 | - | pot1W_f | 176
Corriente | pedida | -908 | - | corriente | leida_W | -909 | 1 | pot0W_g | 38 | - | pot1W_f | 187
Corriente | pedida | -907 | - | corriente | leida_W | -908.03 | 1.03 | pot0W_g | 38 | - | pot1W_f | 197
Corriente | pedida | -906 | - | corriente | leida_W | -906.95 | 0.95 | pot0W_g | 38 | - | pot1W_f | 208
Corriente | pedida | -905 | - | corriente | leida_W | -906 | 1 | pot0W_g | 38 | - | pot1W_f | 218
Corriente | pedida | -904 | - | corriente | leida_W | -904.95 | 0.95 | pot0W_g | 38 | - | pot1W_f | 229
Corriente | pedida | -903 | - | corriente | leida_W | -904 | 1 | pot0W_g | 38 | - | pot1W_f | 239
Corriente | pedida | -902 | - | corriente | leida_W | -902.98 | 0.98 | pot0W_g | 38 | - | pot1W_f | 249
Corriente | pedida | -901 | - | corriente | leida_W | -901.94 | 0.94 | pot0W_g | 39 | - | pot1W_f | 133
Corriente | pedida | -900 | - | corriente | leida_W | -900.97 | 0.97 | pot0W_g | 39 | - | pot1W_f | 143
Corriente | pedida | -899 | - | corriente | leida_W | -900.02 | 1.02 | pot0W_g | 39 | - | pot1W_f | 153
Corriente | pedida | -898 | - | corriente | leida_W | -898.98 | 0.98 | pot0W_g | 39 | - | pot1W_f | 164
Corriente | pedida | -897 | - | corriente | leida_W | -898.02 | 1.02 | pot0W_g | 39 | - | pot1W_f | 174
Corriente | pedida | -896 | - | corriente | leida_W | -896.86 | 0.86 | pot0W_g | 39 | - | pot1W_f | 186
Corriente | pedida | -895 | - | corriente | leida_W | -895.89 | 0.89 | pot0W_g | 39 | - | pot1W_f | 196
Corriente | pedida | -894 | - | corriente | leida_W | -894.97 | 0.97 | pot0W_g | 39 | - | pot1W_f | 206
Corriente | pedida | -893 | - | corriente | leida_W | -893.91 | 0.91 | pot0W_g | 39 | - | pot1W_f | 217
Corriente | pedida | -892 | - | corriente | leida_W | -892.95 | 0.95 | pot0W_g | 39 | - | pot1W_f | 227
Corriente | pedida | -891 | - | corriente | leida_W | -891.94 | 0.94 | pot0W_g | 39 | - | pot1W_f | 237
Corriente | pedida | -890 | - | corriente | leida_W | -890.91 | 0.91 | pot0W_g | 39 | - | pot1W_f | 248
Corriente | pedida | -889 | - | corriente | leida_W | -889.95 | 0.95 | pot0W_g | 40 | - | pot1W_f | 139
Corriente | pedida | -888 | - | corriente | leida_W | -889 | 1 | pot0W_g | 40 | - | pot1W_f | 149
Corriente | pedida | -887 | - | corriente | leida_W | -888.05 | 1.05 | pot0W_g | 40 | - | pot1W_f | 159
Corriente | pedida | -886 | - | corriente | leida_W | -886.98 | 0.98 | pot0W_g | 40 | - | pot1W_f | 170
Corriente | pedida | -885 | - | corriente | leida_W | -886.03 | 1.03 | pot0W_g | 40 | - | pot1W_f | 180
Corriente | pedida | -884 | - | corriente | leida_W | -885 | 1 | pot0W_g | 40 | - | pot1W_f | 191
Corriente | pedida | -883 | - | corriente | leida_W | -884.05 | 1.05 | pot0W_g | 40 | - | pot1W_f | 201
Corriente | pedida | -882 | - | corriente | leida_W | -882.97 | 0.97 | pot0W_g | 40 | - | pot1W_f | 212
Corriente | pedida | -881 | - | corriente | leida_W | -882.03 | 1.03 | pot0W_g | 40 | - | pot1W_f | 222
Corriente | pedida | -880 | - | corriente | leida_W | -880.97 | 0.97 | pot0W_g | 40 | - | pot1W_f | 233
Corriente | pedida | -879 | - | corriente | leida_W | -880 | 1 | pot0W_g | 40 | - | pot1W_f | 243
Corriente | pedida | -878 | - | corriente | leida_W | -878.97 | 0.97 | pot0W_g | 41 | - | pot1W_f | 129
Corriente | pedida | -877 | - | corriente | leida_W | -878 | 1 | pot0W_g | 41 | - | pot1W_f | 139
Corriente | pedida | -876 | - | corriente | leida_W | -877.05 | 1.05 | pot0W_g | 41 | - | pot1W_f | 149
Corriente | pedida | -875 | - | corriente | leida_W | -876 | 1 | pot0W_g | 41 | - | pot1W_f | 160
Corriente | pedida | -874 | - | corriente | leida_W | -875.03 | 1.03 | pot0W_g | 41 | - | pot1W_f | 170
Corriente | pedida | -873 | - | corriente | leida_W | -873.98 | 0.98 | pot0W_g | 41 | - | pot1W_f | 181
Corriente | pedida | -872 | - | corriente | leida_W | -873.03 | 1.03 | pot0W_g | 41 | - | pot1W_f | 191
Corriente | pedida | -871 | - | corriente | leida_W | -871.97 | 0.97 | pot0W_g | 41 | - | pot1W_f | 202
Corriente | pedida | -870 | - | corriente | leida_W | -871.02 | 1.02 | pot0W_g | 41 | - | pot1W_f | 212
Corriente | pedida | -869 | - | corriente | leida_W | -869.98 | 0.98 | pot0W_g | 41 | - | pot1W_f | 223
Corriente | pedida | -868 | - | corriente | leida_W | -869 | 1 | pot0W_g | 41 | - | pot1W_f | 233
Corriente | pedida | -867 | - | corriente | leida_W | -867.95 | 0.95 | pot0W_g | 41 | - | pot1W_f | 244
Corriente | pedida | -866 | - | corriente | leida_W | -866.98 | 0.98 | pot0W_g | 42 | - | pot1W_f | 128
Corriente | pedida | -865 | - | corriente | leida_W | -865.95 | 0.95 | pot0W_g | 42 | - | pot1W_f | 139
Corriente | pedida | -864 | - | corriente | leida_W | -865.02 | 1.02 | pot0W_g | 42 | - | pot1W_f | 149
Corriente | pedida | -863 | - | corriente | leida_W | -864.03 | 1.03 | pot0W_g | 42 | - | pot1W_f | 159
Corriente | pedida | -862 | - | corriente | leida_W | -863 | 1 | pot0W_g | 42 | - | pot1W_f | 170
Corriente | pedida | -861 | - | corriente | leida_W | -862.03 | 1.03 | pot0W_g | 42 | - | pot1W_f | 180
Corriente | pedida | -860 | - | corriente | leida_W | -861 | 1 | pot0W_g | 42 | - | pot1W_f | 191
Corriente | pedida | -859 | - | corriente | leida_W | -859.95 | 0.95 | pot0W_g | 42 | - | pot1W_f | 202
Corriente | pedida | -858 | - | corriente | leida_W | -858.97 | 0.97 | pot0W_g | 42 | - | pot1W_f | 212
Corriente | pedida | -857 | - | corriente | leida_W | -857.94 | 0.94 | pot0W_g | 42 | - | pot1W_f | 223
Corriente | pedida | -856 | - | corriente | leida_W | -856.94 | 0.94 | pot0W_g | 42 | - | pot1W_f | 233
Corriente | pedida | -855 | - | corriente | leida_W | -855.98 | 0.98 | pot0W_g | 42 | - | pot1W_f | 243
Corriente | pedida | -854 | - | corriente | leida_W | -854.94 | 0.94 | pot0W_g | 43 | - | pot1W_f | 132
Corriente | pedida | -853 | - | corriente | leida_W | -854 | 1 | pot0W_g | 43 | - | pot1W_f | 142
Corriente | pedida | -852 | - | corriente | leida_W | -852.92 | 0.92 | pot0W_g | 43 | - | pot1W_f | 153
Corriente | pedida | -851 | - | corriente | leida_W | -851.94 | 0.94 | pot0W_g | 43 | - | pot1W_f | 163
Corriente | pedida | -850 | - | corriente | leida_W | -850.91 | 0.91 | pot0W_g | 43 | - | pot1W_f | 174
Corriente | pedida | -849 | - | corriente | leida_W | -849.94 | 0.94 | pot0W_g | 43 | - | pot1W_f | 184
Corriente | pedida | -848 | - | corriente | leida_W | -848.91 | 0.91 | pot0W_g | 43 | - | pot1W_f | 195
Corriente | pedida | -847 | - | corriente | leida_W | -847.94 | 0.94 | pot0W_g | 43 | - | pot1W_f | 205
Corriente | pedida | -846 | - | corriente | leida_W | -846.97 | 0.97 | pot0W_g | 43 | - | pot1W_f | 215
Corriente | pedida | -845 | - | corriente | leida_W | -845.91 | 0.91 | pot0W_g | 43 | - | pot1W_f | 226
Corriente | pedida | -844 | - | corriente | leida_W | -844.97 | 0.97 | pot0W_g | 43 | - | pot1W_f | 236
Corriente | pedida | -843 | - | corriente | leida_W | -843.91 | 0.91 | pot0W_g | 43 | - | pot1W_f | 247
Corriente | pedida | -842 | - | corriente | leida_W | -842.95 | 0.95 | pot0W_g | 44 | - | pot1W_f | 134
Corriente | pedida | -841 | - | corriente | leida_W | -841.98 | 0.98 | pot0W_g | 44 | - | pot1W_f | 144
Corriente | pedida | -840 | - | corriente | leida_W | -840.95 | 0.95 | pot0W_g | 44 | - | pot1W_f | 155
Corriente | pedida | -839 | - | corriente | leida_W | -839.89 | 0.89 | pot0W_g | 44 | - | pot1W_f | 166
Corriente | pedida | -838 | - | corriente | leida_W | -838.94 | 0.94 | pot0W_g | 44 | - | pot1W_f | 176
Corriente | pedida | -837 | - | corriente | leida_W | -837.89 | 0.89 | pot0W_g | 44 | - | pot1W_f | 187
Corriente | pedida | -836 | - | corriente | leida_W | -836.92 | 0.92 | pot0W_g | 44 | - | pot1W_f | 197
Corriente | pedida | -835 | - | corriente | leida_W | -835.97 | 0.97 | pot0W_g | 44 | - | pot1W_f | 207
Corriente | pedida | -834 | - | corriente | leida_W | -834.94 | 0.94 | pot0W_g | 44 | - | pot1W_f | 218
Corriente | pedida | -833 | - | corriente | leida_W | -833.95 | 0.95 | pot0W_g | 44 | - | pot1W_f | 228
Corriente | pedida | -832 | - | corriente | leida_W | -832.98 | 0.98 | pot0W_g | 44 | - | pot1W_f | 238
Corriente | pedida | -831 | - | corriente | leida_W | -831.94 | 0.94 | pot0W_g | 44 | - | pot1W_f | 249
Corriente | pedida | -830 | - | corriente | leida_W | -830.89 | 0.89 | pot0W_g | 45 | - | pot1W_f | 134
Corriente | pedida | -829 | - | corriente | leida_W | -829.94 | 0.94 | pot0W_g | 45 | - | pot1W_f | 144
Corriente | pedida | -828 | - | corriente | leida_W | -828.97 | 0.97 | pot0W_g | 45 | - | pot1W_f | 154
Corriente | pedida | -827 | - | corriente | leida_W | -827.92 | 0.92 | pot0W_g | 45 | - | pot1W_f | 165
Corriente | pedida | -826 | - | corriente | leida_W | -826.98 | 0.98 | pot0W_g | 45 | - | pot1W_f | 175
Corriente | pedida | -825 | - | corriente | leida_W | -825.94 | 0.94 | pot0W_g | 45 | - | pot1W_f | 186
Corriente | pedida | -824 | - | corriente | leida_W | -824.97 | 0.97 | pot0W_g | 45 | - | pot1W_f | 196
Corriente | pedida | -823 | - | corriente | leida_W | -823.95 | 0.95 | pot0W_g | 45 | - | pot1W_f | 207
Corriente | pedida | -822 | - | corriente | leida_W | -822.98 | 0.98 | pot0W_g | 45 | - | pot1W_f | 217
Corriente | pedida | -821 | - | corriente | leida_W | -821.92 | 0.92 | pot0W_g | 45 | - | pot1W_f | 228
Corriente | pedida | -820 | - | corriente | leida_W | -820.95 | 0.95 | pot0W_g | 45 | - | pot1W_f | 238
Corriente | pedida | -819 | - | corriente | leida_W | -819.98 | 0.98 | pot0W_g | 45 | - | pot1W_f | 248
Corriente | pedida | -818 | - | corriente | leida_W | -818.98 | 0.98 | pot0W_g | 46 | - | pot1W_f | 137
Corriente | pedida | -817 | - | corriente | leida_W | -817.92 | 0.92 | pot0W_g | 46 | - | pot1W_f | 148
Corriente | pedida | -816 | - | corriente | leida_W | -816.95 | 0.95 | pot0W_g | 46 | - | pot1W_f | 158
Corriente | pedida | -815 | - | corriente | leida_W | -815.91 | 0.91 | pot0W_g | 46 | - | pot1W_f | 169
Corriente | pedida | -814 | - | corriente | leida_W | -814.97 | 0.97 | pot0W_g | 46 | - | pot1W_f | 179
Corriente | pedida | -813 | - | corriente | leida_W | -813.89 | 0.89 | pot0W_g | 46 | - | pot1W_f | 190
Corriente | pedida | -812 | - | corriente | leida_W | -812.94 | 0.94 | pot0W_g | 46 | - | pot1W_f | 200
Corriente | pedida | -811 | - | corriente | leida_W | -811.89 | 0.89 | pot0W_g | 46 | - | pot1W_f | 211
Corriente | pedida | -810 | - | corriente | leida_W | -810.91 | 0.91 | pot0W_g | 46 | - | pot1W_f | 221
Corriente | pedida | -809 | - | corriente | leida_W | -809.87 | 0.87 | pot0W_g | 46 | - | pot1W_f | 232
Corriente | pedida | -808 | - | corriente | leida_W | -808.91 | 0.91 | pot0W_g | 46 | - | pot1W_f | 242
Corriente | pedida | -807 | - | corriente | leida_W | -807.92 | 0.92 | pot0W_g | 47 | - | pot1W_f | 131
Corriente | pedida | -806 | - | corriente | leida_W | -806.97 | 0.97 | pot0W_g | 47 | - | pot1W_f | 141
Corriente | pedida | -805 | - | corriente | leida_W | -806.02 | 1.02 | pot0W_g | 47 | - | pot1W_f | 151
Corriente | pedida | -804 | - | corriente | leida_W | -804.97 | 0.97 | pot0W_g | 47 | - | pot1W_f | 162
Corriente | pedida | -803 | - | corriente | leida_W | -804.05 | 1.05 | pot0W_g | 47 | - | pot1W_f | 172
Corriente | pedida | -802 | - | corriente | leida_W | -802.97 | 0.97 | pot0W_g | 47 | - | pot1W_f | 183
Corriente | pedida | -801 | - | corriente | leida_W | -802.03 | 1.03 | pot0W_g | 47 | - | pot1W_f | 193
Corriente | pedida | -800 | - | corriente | leida_W | -801 | 1 | pot0W_g | 47 | - | pot1W_f | 204
Corriente | pedida | -799 | - | corriente | leida_W | -799.98 | 0.98 | pot0W_g | 47 | - | pot1W_f | 214
Corriente | pedida | -798 | - | corriente | leida_W | -799.02 | 1.02 | pot0W_g | 47 | - | pot1W_f | 224
Corriente | pedida | -797 | - | corriente | leida_W | -798 | 1 | pot0W_g | 47 | - | pot1W_f | 235
Corriente | pedida | -796 | - | corriente | leida_W | -797.02 | 1.02 | pot0W_g | 47 | - | pot1W_f | 245
Corriente | pedida | -795 | - | corriente | leida_W | -795.98 | 0.98 | pot0W_g | 48 | - | pot1W_f | 128
Corriente | pedida | -794 | - | corriente | leida_W | -795 | 1 | pot0W_g | 48 | - | pot1W_f | 138
Corriente | pedida | -793 | - | corriente | leida_W | -794.08 | 1.08 | pot0W_g | 48 | - | pot1W_f | 148
Corriente | pedida | -792 | - | corriente | leida_W | -793.08 | 1.08 | pot0W_g | 48 | - | pot1W_f | 158
Corriente | pedida | -791 | - | corriente | leida_W | -792.06 | 1.06 | pot0W_g | 48 | - | pot1W_f | 169
Corriente | pedida | -790 | - | corriente | leida_W | -791 | 1 | pot0W_g | 48 | - | pot1W_f | 180
Corriente | pedida | -789 | - | corriente | leida_W | -790.06 | 1.06 | pot0W_g | 48 | - | pot1W_f | 190
Corriente | pedida | -788 | - | corriente | leida_W | -789.11 | 1.11 | pot0W_g | 48 | - | pot1W_f | 200
Corriente | pedida | -787 | - | corriente | leida_W | -788.03 | 1.03 | pot0W_g | 48 | - | pot1W_f | 211
Corriente | pedida | -786 | - | corriente | leida_W | -787.08 | 1.08 | pot0W_g | 48 | - | pot1W_f | 221
Corriente | pedida | -785 | - | corriente | leida_W | -786.03 | 1.03 | pot0W_g | 48 | - | pot1W_f | 232
Corriente | pedida | -784 | - | corriente | leida_W | -785.06 | 1.06 | pot0W_g | 48 | - | pot1W_f | 242
Corriente | pedida | -783 | - | corriente | leida_W | -784 | 1 | pot0W_g | 49 | - | pot1W_f | 134
Corriente | pedida | -782 | - | corriente | leida_W | -783.05 | 1.05 | pot0W_g | 49 | - | pot1W_f | 144
Corriente | pedida | -781 | - | corriente | leida_W | -782.08 | 1.08 | pot0W_g | 49 | - | pot1W_f | 154
Corriente | pedida | -780 | - | corriente | leida_W | -781.06 | 1.06 | pot0W_g | 49 | - | pot1W_f | 165
Corriente | pedida | -779 | - | corriente | leida_W | -780.09 | 1.09 | pot0W_g | 49 | - | pot1W_f | 175
Corriente | pedida | -778 | - | corriente | leida_W | -779.06 | 1.06 | pot0W_g | 49 | - | pot1W_f | 186
Corriente | pedida | -777 | - | corriente | leida_W | -778.11 | 1.11 | pot0W_g | 49 | - | pot1W_f | 196
Corriente | pedida | -776 | - | corriente | leida_W | -777.09 | 1.09 | pot0W_g | 49 | - | pot1W_f | 207
Corriente | pedida | -775 | - | corriente | leida_W | -776 | 1 | pot0W_g | 49 | - | pot1W_f | 218
Corriente | pedida | -774 | - | corriente | leida_W | -775.02 | 1.02 | pot0W_g | 49 | - | pot1W_f | 228
Corriente | pedida | -773 | - | corriente | leida_W | -774.06 | 1.06 | pot0W_g | 49 | - | pot1W_f | 238
Corriente | pedida | -772 | - | corriente | leida_W | -773 | 1 | pot0W_g | 49 | - | pot1W_f | 249
Corriente | pedida | -771 | - | corriente | leida_W | -771.95 | 0.95 | pot0W_g | 50 | - | pot1W_f | 140
Corriente | pedida | -770 | - | corriente | leida_W | -770.98 | 0.98 | pot0W_g | 50 | - | pot1W_f | 150
Corriente | pedida | -769 | - | corriente | leida_W | -770.03 | 1.03 | pot0W_g | 50 | - | pot1W_f | 160
Corriente | pedida | -768 | - | corriente | leida_W | -768.98 | 0.98 | pot0W_g | 50 | - | pot1W_f | 171
Corriente | pedida | -767 | - | corriente | leida_W | -768.03 | 1.03 | pot0W_g | 50 | - | pot1W_f | 181
Corriente | pedida | -766 | - | corriente | leida_W | -766.98 | 0.98 | pot0W_g | 50 | - | pot1W_f | 192
Corriente | pedida | -765 | - | corriente | leida_W | -766.03 | 1.03 | pot0W_g | 50 | - | pot1W_f | 202
Corriente | pedida | -764 | - | corriente | leida_W | -764.98 | 0.98 | pot0W_g | 50 | - | pot1W_f | 213
Corriente | pedida | -763 | - | corriente | leida_W | -764.03 | 1.03 | pot0W_g | 50 | - | pot1W_f | 223
Corriente | pedida | -762 | - | corriente | leida_W | -763.06 | 1.06 | pot0W_g | 50 | - | pot1W_f | 233
Corriente | pedida | -761 | - | corriente | leida_W | -762.19 | 1.19 | pot0W_g | 50 | - | pot1W_f | 242
Corriente | pedida | -760 | - | corriente | leida_W | -761.19 | 1.19 | pot0W_g | 51 | - | pot1W_f | 136
Corriente | pedida | -759 | - | corriente | leida_W | -760.23 | 1.23 | pot0W_g | 51 | - | pot1W_f | 146
Corriente | pedida | -758 | - | corriente | leida_W | -759.16 | 1.16 | pot0W_g | 51 | - | pot1W_f | 157
Corriente | pedida | -757 | - | corriente | leida_W | -758.19 | 1.19 | pot0W_g | 51 | - | pot1W_f | 167
Corriente | pedida | -756 | - | corriente | leida_W | -757.17 | 1.17 | pot0W_g | 51 | - | pot1W_f | 178
Corriente | pedida | -755 | - | corriente | leida_W | -756.22 | 1.22 | pot0W_g | 51 | - | pot1W_f | 188
Corriente | pedida | -754 | - | corriente | leida_W | -755.17 | 1.17 | pot0W_g | 51 | - | pot1W_f | 199
Corriente | pedida | -753 | - | corriente | leida_W | -754.2 | 1.2 | pot0W_g | 51 | - | pot1W_f | 209
Corriente | pedida | -752 | - | corriente | leida_W | -753.14 | 1.14 | pot0W_g | 51 | - | pot1W_f | 220
Corriente | pedida | -751 | - | corriente | leida_W | -752.19 | 1.19 | pot0W_g | 51 | - | pot1W_f | 230
Corriente | pedida | -750 | - | corriente | leida_W | -751.2 | 1.2 | pot0W_g | 51 | - | pot1W_f | 240
Corriente | pedida | -749 | - | corriente | leida_W | -750.22 | 1.22 | pot0W_g | 52 | - | pot1W_f | 133
Corriente | pedida | -748 | - | corriente | leida_W | -749.28 | 1.28 | pot0W_g | 52 | - | pot1W_f | 143
Corriente | pedida | -747 | - | corriente | leida_W | -748.22 | 1.22 | pot0W_g | 52 | - | pot1W_f | 154
Corriente | pedida | -746 | - | corriente | leida_W | -747.22 | 1.22 | pot0W_g | 52 | - | pot1W_f | 164
Corriente | pedida | -745 | - | corriente | leida_W | -746.3 | 1.3 | pot0W_g | 52 | - | pot1W_f | 174
Corriente | pedida | -744 | - | corriente | leida_W | -745.25 | 1.25 | pot0W_g | 52 | - | pot1W_f | 185
Corriente | pedida | -743 | - | corriente | leida_W | -744.3 | 1.3 | pot0W_g | 52 | - | pot1W_f | 195
Corriente | pedida | -742 | - | corriente | leida_W | -743.22 | 1.22 | pot0W_g | 52 | - | pot1W_f | 206
Corriente | pedida | -741 | - | corriente | leida_W | -742.17 | 1.17 | pot0W_g | 52 | - | pot1W_f | 217
Corriente | pedida | -740 | - | corriente | leida_W | -741.22 | 1.22 | pot0W_g | 52 | - | pot1W_f | 227
Corriente | pedida | -739 | - | corriente | leida_W | -740.25 | 1.25 | pot0W_g | 52 | - | pot1W_f | 237
Corriente | pedida | -738 | - | corriente | leida_W | -739.28 | 1.28 | pot0W_g | 52 | - | pot1W_f | 247
Corriente | pedida | -737 | - | corriente | leida_W | -738.23 | 1.23 | pot0W_g | 53 | - | pot1W_f | 138
Corriente | pedida | -736 | - | corriente | leida_W | -737.28 | 1.28 | pot0W_g | 53 | - | pot1W_f | 148
Corriente | pedida | -735 | - | corriente | leida_W | -736.23 | 1.23 | pot0W_g | 53 | - | pot1W_f | 159
Corriente | pedida | -734 | - | corriente | leida_W | -735.27 | 1.27 | pot0W_g | 53 | - | pot1W_f | 169
Corriente | pedida | -733 | - | corriente | leida_W | -734.33 | 1.33 | pot0W_g | 53 | - | pot1W_f | 179
Corriente | pedida | -732 | - | corriente | leida_W | -733.27 | 1.27 | pot0W_g | 53 | - | pot1W_f | 190
Corriente | pedida | -731 | - | corriente | leida_W | -732.22 | 1.22 | pot0W_g | 53 | - | pot1W_f | 201
Corriente | pedida | -730 | - | corriente | leida_W | -731.37 | 1.37 | pot0W_g | 53 | - | pot1W_f | 210
Corriente | pedida | -729 | - | corriente | leida_W | -730.42 | 1.42 | pot0W_g | 53 | - | pot1W_f | 220
Corriente | pedida | -728 | - | corriente | leida_W | -729.34 | 1.34 | pot0W_g | 53 | - | pot1W_f | 231
Corriente | pedida | -727 | - | corriente | leida_W | -728.34 | 1.34 | pot0W_g | 53 | - | pot1W_f | 241
Corriente | pedida | -726 | - | corriente | leida_W | -727.39 | 1.39 | pot0W_g | 54 | - | pot1W_f | 135
Corriente | pedida | -725 | - | corriente | leida_W | -726.44 | 1.44 | pot0W_g | 54 | - | pot1W_f | 145
Corriente | pedida | -724 | - | corriente | leida_W | -725.37 | 1.37 | pot0W_g | 54 | - | pot1W_f | 156
Corriente | pedida | -723 | - | corriente | leida_W | -724.44 | 1.44 | pot0W_g | 54 | - | pot1W_f | 166
Corriente | pedida | -722 | - | corriente | leida_W | -723.36 | 1.36 | pot0W_g | 54 | - | pot1W_f | 177
Corriente | pedida | -721 | - | corriente | leida_W | -722.31 | 1.31 | pot0W_g | 54 | - | pot1W_f | 188
Corriente | pedida | -720 | - | corriente | leida_W | -721.36 | 1.36 | pot0W_g | 54 | - | pot1W_f | 198
Corriente | pedida | -719 | - | corriente | leida_W | -720.41 | 1.41 | pot0W_g | 54 | - | pot1W_f | 208
Corriente | pedida | -718 | - | corriente | leida_W | -719.36 | 1.36 | pot0W_g | 54 | - | pot1W_f | 219
Corriente | pedida | -717 | - | corriente | leida_W | -718.37 | 1.37 | pot0W_g | 54 | - | pot1W_f | 229
Corriente | pedida | -716 | - | corriente | leida_W | -717.33 | 1.33 | pot0W_g | 54 | - | pot1W_f | 240
Corriente | pedida | -715 | - | corriente | leida_W | -716.37 | 1.37 | pot0W_g | 55 | - | pot1W_f | 134
Corriente | pedida | -714 | - | corriente | leida_W | -715.31 | 1.31 | pot0W_g | 55 | - | pot1W_f | 145
Corriente | pedida | -713 | - | corriente | leida_W | -714.33 | 1.33 | pot0W_g | 55 | - | pot1W_f | 155
Corriente | pedida | -712 | - | corriente | leida_W | -713.41 | 1.41 | pot0W_g | 55 | - | pot1W_f | 165
Corriente | pedida | -711 | - | corriente | leida_W | -712.34 | 1.34 | pot0W_g | 55 | - | pot1W_f | 176
Corriente | pedida | -710 | - | corriente | leida_W | -711.5 | 1.5 | pot0W_g | 55 | - | pot1W_f | 185
Corriente | pedida | -709 | - | corriente | leida_W | -710.55 | 1.55 | pot0W_g | 55 | - | pot1W_f | 195
Corriente | pedida | -708 | - | corriente | leida_W | -709.5 | 1.5 | pot0W_g | 55 | - | pot1W_f | 206
Corriente | pedida | -707 | - | corriente | leida_W | -708.52 | 1.52 | pot0W_g | 55 | - | pot1W_f | 216
Corriente | pedida | -706 | - | corriente | leida_W | -707.55 | 1.55 | pot0W_g | 55 | - | pot1W_f | 226
Corriente | pedida | -705 | - | corriente | leida_W | -706.58 | 1.58 | pot0W_g | 55 | - | pot1W_f | 236
Corriente | pedida | -704 | - | corriente | leida_W | -705.55 | 1.55 | pot0W_g | 55 | - | pot1W_f | 247
Corriente | pedida | -703 | - | corriente | leida_W | -704.47 | 1.47 | pot0W_g | 56 | - | pot1W_f | 140
Corriente | pedida | -702 | - | corriente | leida_W | -703.52 | 1.52 | pot0W_g | 56 | - | pot1W_f | 150
Corriente | pedida | -701 | - | corriente | leida_W | -702.5 | 1.5 | pot0W_g | 56 | - | pot1W_f | 160
Corriente | pedida | -700 | - | corriente | leida_W | -701.48 | 1.48 | pot0W_g | 56 | - | pot1W_f | 171
Corriente | pedida | -699 | - | corriente | leida_W | -700.42 | 1.42 | pot0W_g | 56 | - | pot1W_f | 182
Corriente | pedida | -698 | - | corriente | leida_W | -699.5 | 1.5 | pot0W_g | 56 | - | pot1W_f | 192
Corriente | pedida | -697 | - | corriente | leida_W | -698.44 | 1.44 | pot0W_g | 56 | - | pot1W_f | 203
Corriente | pedida | -696 | - | corriente | leida_W | -697.47 | 1.47 | pot0W_g | 56 | - | pot1W_f | 213
Corriente | pedida | -695 | - | corriente | leida_W | -696.42 | 1.42 | pot0W_g | 56 | - | pot1W_f | 224
Corriente | pedida | -694 | - | corriente | leida_W | -695.55 | 1.55 | pot0W_g | 56 | - | pot1W_f | 233
Corriente | pedida | -693 | - | corriente | leida_W | -694.58 | 1.58 | pot0W_g | 56 | - | pot1W_f | 243
Corriente | pedida | -692 | - | corriente | leida_W | -693.53 | 1.53 | pot0W_g | 57 | - | pot1W_f | 140
Corriente | pedida | -691 | - | corriente | leida_W | -692.59 | 1.59 | pot0W_g | 57 | - | pot1W_f | 150
Corriente | pedida | -690 | - | corriente | leida_W | -691.61 | 1.61 | pot0W_g | 57 | - | pot1W_f | 160
Corriente | pedida | -689 | - | corriente | leida_W | -690.56 | 1.56 | pot0W_g | 57 | - | pot1W_f | 171
Corriente | pedida | -688 | - | corriente | leida_W | -689.52 | 1.52 | pot0W_g | 57 | - | pot1W_f | 182
Corriente | pedida | -687 | - | corriente | leida_W | -688.55 | 1.55 | pot0W_g | 57 | - | pot1W_f | 192
Corriente | pedida | -686 | - | corriente | leida_W | -687.52 | 1.52 | pot0W_g | 57 | - | pot1W_f | 203
Corriente | pedida | -685 | - | corriente | leida_W | -686.55 | 1.55 | pot0W_g | 57 | - | pot1W_f | 213
Corriente | pedida | -684 | - | corriente | leida_W | -685.48 | 1.48 | pot0W_g | 57 | - | pot1W_f | 224
Corriente | pedida | -683 | - | corriente | leida_W | -684.52 | 1.52 | pot0W_g | 57 | - | pot1W_f | 234
Corriente | pedida | -682 | - | corriente | leida_W | -683.47 | 1.47 | pot0W_g | 57 | - | pot1W_f | 245
Corriente | pedida | -681 | - | corriente | leida_W | -682.44 | 1.44 | pot0W_g | 58 | - | pot1W_f | 141
Corriente | pedida | -680 | - | corriente | leida_W | -681.48 | 1.48 | pot0W_g | 58 | - | pot1W_f | 151
Corriente | pedida | -679 | - | corriente | leida_W | -680.48 | 1.48 | pot0W_g | 58 | - | pot1W_f | 161
Corriente | pedida | -678 | - | corriente | leida_W | -679.45 | 1.45 | pot0W_g | 58 | - | pot1W_f | 172
Corriente | pedida | -677 | - | corriente | leida_W | -678.5 | 1.5 | pot0W_g | 58 | - | pot1W_f | 182
Corriente | pedida | -676 | - | corriente | leida_W | -677.55 | 1.55 | pot0W_g | 58 | - | pot1W_f | 192
Corriente | pedida | -675 | - | corriente | leida_W | -676.5 | 1.5 | pot0W_g | 58 | - | pot1W_f | 203
Corriente | pedida | -674 | - | corriente | leida_W | -675.44 | 1.44 | pot0W_g | 58 | - | pot1W_f | 214
Corriente | pedida | -673 | - | corriente | leida_W | -674.5 | 1.5 | pot0W_g | 58 | - | pot1W_f | 224
Corriente | pedida | -672 | - | corriente | leida_W | -673.5 | 1.5 | pot0W_g | 58 | - | pot1W_f | 234
Corriente | pedida | -671 | - | corriente | leida_W | -672.44 | 1.44 | pot0W_g | 58 | - | pot1W_f | 245
Corriente | pedida | -670 | - | corriente | leida_W | -671.42 | 1.42 | pot0W_g | 59 | - | pot1W_f | 144
Corriente | pedida | -669 | - | corriente | leida_W | -670.47 | 1.47 | pot0W_g | 59 | - | pot1W_f | 154
Corriente | pedida | -668 | - | corriente | leida_W | -669.5 | 1.5 | pot0W_g | 59 | - | pot1W_f | 164
Corriente | pedida | -667 | - | corriente | leida_W | -668.47 | 1.47 | pot0W_g | 59 | - | pot1W_f | 175
Corriente | pedida | -666 | - | corriente | leida_W | -667.52 | 1.52 | pot0W_g | 59 | - | pot1W_f | 185
Corriente | pedida | -665 | - | corriente | leida_W | -666.56 | 1.56 | pot0W_g | 59 | - | pot1W_f | 195
Corriente | pedida | -664 | - | corriente | leida_W | -665.48 | 1.48 | pot0W_g | 59 | - | pot1W_f | 206
Corriente | pedida | -663 | - | corriente | leida_W | -664.53 | 1.53 | pot0W_g | 59 | - | pot1W_f | 216
Corriente | pedida | -662 | - | corriente | leida_W | -663.47 | 1.47 | pot0W_g | 59 | - | pot1W_f | 227
Corriente | pedida | -661 | - | corriente | leida_W | -662.52 | 1.52 | pot0W_g | 59 | - | pot1W_f | 237
Corriente | pedida | -660 | - | corriente | leida_W | -661.47 | 1.47 | pot0W_g | 59 | - | pot1W_f | 248
Corriente | pedida | -659 | - | corriente | leida_W | -660.44 | 1.44 | pot0W_g | 60 | - | pot1W_f | 146
Corriente | pedida | -658 | - | corriente | leida_W | -659.5 | 1.5 | pot0W_g | 60 | - | pot1W_f | 156
Corriente | pedida | -657 | - | corriente | leida_W | -658.44 | 1.44 | pot0W_g | 60 | - | pot1W_f | 167
Corriente | pedida | -656 | - | corriente | leida_W | -657.48 | 1.48 | pot0W_g | 60 | - | pot1W_f | 177
Corriente | pedida | -655 | - | corriente | leida_W | -656.44 | 1.44 | pot0W_g | 60 | - | pot1W_f | 188
Corriente | pedida | -654 | - | corriente | leida_W | -655.45 | 1.45 | pot0W_g | 60 | - | pot1W_f | 198
Corriente | pedida | -653 | - | corriente | leida_W | -654.52 | 1.52 | pot0W_g | 60 | - | pot1W_f | 208
Corriente | pedida | -652 | - | corriente | leida_W | -653.47 | 1.47 | pot0W_g | 60 | - | pot1W_f | 219
Corriente | pedida | -651 | - | corriente | leida_W | -652.52 | 1.52 | pot0W_g | 60 | - | pot1W_f | 229
Corriente | pedida | -650 | - | corriente | leida_W | -651.44 | 1.44 | pot0W_g | 60 | - | pot1W_f | 240
Corriente | pedida | -649 | - | corriente | leida_W | -650.47 | 1.47 | pot0W_g | 61 | - | pot1W_f | 135
Corriente | pedida | -648 | - | corriente | leida_W | -649.5 | 1.5 | pot0W_g | 61 | - | pot1W_f | 145
Corriente | pedida | -647 | - | corriente | leida_W | -648.45 | 1.45 | pot0W_g | 61 | - | pot1W_f | 156
Corriente | pedida | -646 | - | corriente | leida_W | -647.52 | 1.52 | pot0W_g | 61 | - | pot1W_f | 166
Corriente | pedida | -645 | - | corriente | leida_W | -646.45 | 1.45 | pot0W_g | 61 | - | pot1W_f | 177
Corriente | pedida | -644 | - | corriente | leida_W | -645.41 | 1.41 | pot0W_g | 61 | - | pot1W_f | 188
Corriente | pedida | -643 | - | corriente | leida_W | -644.47 | 1.47 | pot0W_g | 61 | - | pot1W_f | 198
Corriente | pedida | -642 | - | corriente | leida_W | -643.41 | 1.41 | pot0W_g | 61 | - | pot1W_f | 209
Corriente | pedida | -641 | - | corriente | leida_W | -642.44 | 1.44 | pot0W_g | 61 | - | pot1W_f | 219
Corriente | pedida | -640 | - | corriente | leida_W | -641.41 | 1.41 | pot0W_g | 61 | - | pot1W_f | 230
Corriente | pedida | -639 | - | corriente | leida_W | -640.31 | 1.31 | pot0W_g | 61 | - | pot1W_f | 241
Corriente | pedida | -638 | - | corriente | leida_W | -639.31 | 1.31 | pot0W_g | 62 | - | pot1W_f | 140
Corriente | pedida | -637 | - | corriente | leida_W | -638.44 | 1.44 | pot0W_g | 62 | - | pot1W_f | 149
Corriente | pedida | -636 | - | corriente | leida_W | -637.37 | 1.37 | pot0W_g | 62 | - | pot1W_f | 160
Corriente | pedida | -635 | - | corriente | leida_W | -636.44 | 1.44 | pot0W_g | 62 | - | pot1W_f | 170
Corriente | pedida | -634 | - | corriente | leida_W | -635.39 | 1.39 | pot0W_g | 62 | - | pot1W_f | 181
Corriente | pedida | -633 | - | corriente | leida_W | -634.44 | 1.44 | pot0W_g | 62 | - | pot1W_f | 191
Corriente | pedida | -632 | - | corriente | leida_W | -633.48 | 1.48 | pot0W_g | 62 | - | pot1W_f | 201
Corriente | pedida | -631 | - | corriente | leida_W | -632.44 | 1.44 | pot0W_g | 62 | - | pot1W_f | 212
Corriente | pedida | -630 | - | corriente | leida_W | -631.47 | 1.47 | pot0W_g | 62 | - | pot1W_f | 222
Corriente | pedida | -629 | - | corriente | leida_W | -630.48 | 1.48 | pot0W_g | 62 | - | pot1W_f | 232
Corriente | pedida | -628 | - | corriente | leida_W | -629.44 | 1.44 | pot0W_g | 62 | - | pot1W_f | 243
Corriente | pedida | -627 | - | corriente | leida_W | -628.45 | 1.45 | pot0W_g | 63 | - | pot1W_f | 142
Corriente | pedida | -626 | - | corriente | leida_W | -627.47 | 1.47 | pot0W_g | 63 | - | pot1W_f | 152
Corriente | pedida | -625 | - | corriente | leida_W | -626.42 | 1.42 | pot0W_g | 63 | - | pot1W_f | 163
Corriente | pedida | -624 | - | corriente | leida_W | -625.48 | 1.48 | pot0W_g | 63 | - | pot1W_f | 173
Corriente | pedida | -623 | - | corriente | leida_W | -624.44 | 1.44 | pot0W_g | 63 | - | pot1W_f | 184
Corriente | pedida | -622 | - | corriente | leida_W | -623.37 | 1.37 | pot0W_g | 63 | - | pot1W_f | 195
Corriente | pedida | -621 | - | corriente | leida_W | -622.41 | 1.41 | pot0W_g | 63 | - | pot1W_f | 205
Corriente | pedida | -620 | - | corriente | leida_W | -621.36 | 1.36 | pot0W_g | 63 | - | pot1W_f | 216
Corriente | pedida | -619 | - | corriente | leida_W | -620.41 | 1.41 | pot0W_g | 63 | - | pot1W_f | 226
Corriente | pedida | -618 | - | corriente | leida_W | -619.34 | 1.34 | pot0W_g | 63 | - | pot1W_f | 237
Corriente | pedida | -617 | - | corriente | leida_W | -618.28 | 1.28 | pot0W_g | 63 | - | pot1W_f | 248
Corriente | pedida | -616 | - | corriente | leida_W | -617.19 | 1.19 | pot0W_g | 64 | - | pot1W_f | 155
Corriente | pedida | -615 | - | corriente | leida_W | -616.23 | 1.23 | pot0W_g | 64 | - | pot1W_f | 165
Corriente | pedida | -614 | - | corriente | leida_W | -615.2 | 1.2 | pot0W_g | 64 | - | pot1W_f | 176
Corriente | pedida | -613 | - | corriente | leida_W | -614.14 | 1.14 | pot0W_g | 64 | - | pot1W_f | 187
Corriente | pedida | -612 | - | corriente | leida_W | -613.19 | 1.19 | pot0W_g | 64 | - | pot1W_f | 197
Corriente | pedida | -611 | - | corriente | leida_W | -612.22 | 1.22 | pot0W_g | 64 | - | pot1W_f | 207
Corriente | pedida | -610 | - | corriente | leida_W | -611.27 | 1.27 | pot0W_g | 64 | - | pot1W_f | 217
Corriente | pedida | -609 | - | corriente | leida_W | -610.31 | 1.31 | pot0W_g | 64 | - | pot1W_f | 227
Corriente | pedida | -608 | - | corriente | leida_W | -609.27 | 1.27 | pot0W_g | 64 | - | pot1W_f | 238
Corriente | pedida | -607 | - | corriente | leida_W | -608.2 | 1.2 | pot0W_g | 64 | - | pot1W_f | 249
Corriente | pedida | -606 | - | corriente | leida_W | -607.17 | 1.17 | pot0W_g | 65 | - | pot1W_f | 150
Corriente | pedida | -605 | - | corriente | leida_W | -606.19 | 1.19 | pot0W_g | 65 | - | pot1W_f | 160
Corriente | pedida | -604 | - | corriente | leida_W | -605.16 | 1.16 | pot0W_g | 65 | - | pot1W_f | 171
Corriente | pedida | -603 | - | corriente | leida_W | -604.2 | 1.2 | pot0W_g | 65 | - | pot1W_f | 181
Corriente | pedida | -602 | - | corriente | leida_W | -603.14 | 1.14 | pot0W_g | 65 | - | pot1W_f | 192
Corriente | pedida | -601 | - | corriente | leida_W | -602.19 | 1.19 | pot0W_g | 65 | - | pot1W_f | 202
Corriente | pedida | -600 | - | corriente | leida_W | -601.23 | 1.23 | pot0W_g | 65 | - | pot1W_f | 212
Corriente | pedida | -599 | - | corriente | leida_W | -600.2 | 1.2 | pot0W_g | 65 | - | pot1W_f | 223
Corriente | pedida | -598 | - | corriente | leida_W | -599.11 | 1.11 | pot0W_g | 65 | - | pot1W_f | 234
Corriente | pedida | -597 | - | corriente | leida_W | -598.12 | 1.12 | pot0W_g | 65 | - | pot1W_f | 244
Corriente | pedida | -596 | - | corriente | leida_W | -597.16 | 1.16 | pot0W_g | 66 | - | pot1W_f | 144
Corriente | pedida | -595 | - | corriente | leida_W | -596.16 | 1.16 | pot0W_g | 66 | - | pot1W_f | 154
Corriente | pedida | -594 | - | corriente | leida_W | -595.12 | 1.12 | pot0W_g | 66 | - | pot1W_f | 165
Corriente | pedida | -593 | - | corriente | leida_W | -594.06 | 1.06 | pot0W_g | 66 | - | pot1W_f | 176
Corriente | pedida | -592 | - | corriente | leida_W | -593.14 | 1.14 | pot0W_g | 66 | - | pot1W_f | 186
Corriente | pedida | -591 | - | corriente | leida_W | -592.08 | 1.08 | pot0W_g | 66 | - | pot1W_f | 197
Corriente | pedida | -590 | - | corriente | leida_W | -591.09 | 1.09 | pot0W_g | 66 | - | pot1W_f | 207
Corriente | pedida | -589 | - | corriente | leida_W | -590.06 | 1.06 | pot0W_g | 66 | - | pot1W_f | 218
Corriente | pedida | -588 | - | corriente | leida_W | -589.12 | 1.12 | pot0W_g | 66 | - | pot1W_f | 228
Corriente | pedida | -587 | - | corriente | leida_W | -588.16 | 1.16 | pot0W_g | 66 | - | pot1W_f | 238
Corriente | pedida | -586 | - | corriente | leida_W | -587.09 | 1.09 | pot0W_g | 66 | - | pot1W_f | 249
Corriente | pedida | -585 | - | corriente | leida_W | -586.03 | 1.03 | pot0W_g | 67 | - | pot1W_f | 152
Corriente | pedida | -584 | - | corriente | leida_W | -585.06 | 1.06 | pot0W_g | 67 | - | pot1W_f | 162
Corriente | pedida | -583 | - | corriente | leida_W | -584.03 | 1.03 | pot0W_g | 67 | - | pot1W_f | 173
Corriente | pedida | -582 | - | corriente | leida_W | -583.06 | 1.06 | pot0W_g | 67 | - | pot1W_f | 183
Corriente | pedida | -581 | - | corriente | leida_W | -582.02 | 1.02 | pot0W_g | 67 | - | pot1W_f | 194
Corriente | pedida | -580 | - | corriente | leida_W | -581.06 | 1.06 | pot0W_g | 67 | - | pot1W_f | 204
Corriente | pedida | -579 | - | corriente | leida_W | -580.12 | 1.12 | pot0W_g | 67 | - | pot1W_f | 214
Corriente | pedida | -578 | - | corriente | leida_W | -579.05 | 1.05 | pot0W_g | 67 | - | pot1W_f | 225
Corriente | pedida | -577 | - | corriente | leida_W | -578.09 | 1.09 | pot0W_g | 67 | - | pot1W_f | 235
Corriente | pedida | -576 | - | corriente | leida_W | -577.02 | 1.02 | pot0W_g | 67 | - | pot1W_f | 246
Corriente | pedida | -575 | - | corriente | leida_W | -576.02 | 1.02 | pot0W_g | 68 | - | pot1W_f | 148
Corriente | pedida | -574 | - | corriente | leida_W | -575.08 | 1.08 | pot0W_g | 68 | - | pot1W_f | 158
Corriente | pedida | -573 | - | corriente | leida_W | -574.14 | 1.14 | pot0W_g | 68 | - | pot1W_f | 168
Corriente | pedida | -572 | - | corriente | leida_W | -573.05 | 1.05 | pot0W_g | 68 | - | pot1W_f | 179
Corriente | pedida | -571 | - | corriente | leida_W | -572.11 | 1.11 | pot0W_g | 68 | - | pot1W_f | 189
Corriente | pedida | -570 | - | corriente | leida_W | -571.06 | 1.06 | pot0W_g | 68 | - | pot1W_f | 200
Corriente | pedida | -569 | - | corriente | leida_W | -570.09 | 1.09 | pot0W_g | 68 | - | pot1W_f | 210
Corriente | pedida | -568 | - | corriente | leida_W | -569.05 | 1.05 | pot0W_g | 68 | - | pot1W_f | 221
Corriente | pedida | -567 | - | corriente | leida_W | -568.09 | 1.09 | pot0W_g | 68 | - | pot1W_f | 231
Corriente | pedida | -566 | - | corriente | leida_W | -567.02 | 1.02 | pot0W_g | 68 | - | pot1W_f | 242
Corriente | pedida | -565 | - | corriente | leida_W | -565.98 | 0.98 | pot0W_g | 69 | - | pot1W_f | 142
Corriente | pedida | -564 | - | corriente | leida_W | -565 | 1 | pot0W_g | 69 | - | pot1W_f | 152
Corriente | pedida | -563 | - | corriente | leida_W | -564.05 | 1.05 | pot0W_g | 69 | - | pot1W_f | 162
Corriente | pedida | -562 | - | corriente | leida_W | -563.06 | 1.06 | pot0W_g | 69 | - | pot1W_f | 172
Corriente | pedida | -561 | - | corriente | leida_W | -562.03 | 1.03 | pot0W_g | 69 | - | pot1W_f | 183
Corriente | pedida | -560 | - | corriente | leida_W | -560.95 | 0.95 | pot0W_g | 69 | - | pot1W_f | 194
Corriente | pedida | -559 | - | corriente | leida_W | -560.03 | 1.03 | pot0W_g | 69 | - | pot1W_f | 204
Corriente | pedida | -558 | - | corriente | leida_W | -559.08 | 1.08 | pot0W_g | 69 | - | pot1W_f | 214
Corriente | pedida | -557 | - | corriente | leida_W | -558.02 | 1.02 | pot0W_g | 69 | - | pot1W_f | 225
Corriente | pedida | -556 | - | corriente | leida_W | -557.05 | 1.05 | pot0W_g | 69 | - | pot1W_f | 235
Corriente | pedida | -555 | - | corriente | leida_W | -556 | 1 | pot0W_g | 69 | - | pot1W_f | 246
Corriente | pedida | -554 | - | corriente | leida_W | -554.97 | 0.97 | pot0W_g | 70 | - | pot1W_f | 149
Corriente | pedida | -553 | - | corriente | leida_W | -554.02 | 1.02 | pot0W_g | 70 | - | pot1W_f | 159
Corriente | pedida | -552 | - | corriente | leida_W | -553.06 | 1.06 | pot0W_g | 70 | - | pot1W_f | 169
Corriente | pedida | -551 | - | corriente | leida_W | -552 | 1 | pot0W_g | 70 | - | pot1W_f | 180
Corriente | pedida | -550 | - | corriente | leida_W | -551.05 | 1.05 | pot0W_g | 70 | - | pot1W_f | 190
Corriente | pedida | -549 | - | corriente | leida_W | -550 | 1 | pot0W_g | 70 | - | pot1W_f | 201
Corriente | pedida | -548 | - | corriente | leida_W | -549.03 | 1.03 | pot0W_g | 70 | - | pot1W_f | 211
Corriente | pedida | -547 | - | corriente | leida_W | -548.09 | 1.09 | pot0W_g | 70 | - | pot1W_f | 221
Corriente | pedida | -546 | - | corriente | leida_W | -547 | 1 | pot0W_g | 70 | - | pot1W_f | 232
Corriente | pedida | -545 | - | corriente | leida_W | -546.03 | 1.03 | pot0W_g | 70 | - | pot1W_f | 242
Corriente | pedida | -544 | - | corriente | leida_W | -545.03 | 1.03 | pot0W_g | 71 | - | pot1W_f | 145
Corriente | pedida | -543 | - | corriente | leida_W | -544.05 | 1.05 | pot0W_g | 71 | - | pot1W_f | 155
Corriente | pedida | -542 | - | corriente | leida_W | -543.02 | 1.02 | pot0W_g | 71 | - | pot1W_f | 166
Corriente | pedida | -541 | - | corriente | leida_W | -542.06 | 1.06 | pot0W_g | 71 | - | pot1W_f | 176
Corriente | pedida | -540 | - | corriente | leida_W | -541.03 | 1.03 | pot0W_g | 71 | - | pot1W_f | 187
Corriente | pedida | -539 | - | corriente | leida_W | -540.05 | 1.05 | pot0W_g | 71 | - | pot1W_f | 197
Corriente | pedida | -538 | - | corriente | leida_W | -539.08 | 1.08 | pot0W_g | 71 | - | pot1W_f | 207
Corriente | pedida | -537 | - | corriente | leida_W | -538.05 | 1.05 | pot0W_g | 71 | - | pot1W_f | 218
Corriente | pedida | -536 | - | corriente | leida_W | -537.02 | 1.02 | pot0W_g | 71 | - | pot1W_f | 229
Corriente | pedida | -535 | - | corriente | leida_W | -535.92 | 0.92 | pot0W_g | 71 | - | pot1W_f | 240
Corriente | pedida | -534 | - | corriente | leida_W | -534.95 | 0.95 | pot0W_g | 72 | - | pot1W_f | 145
Corriente | pedida | -533 | - | corriente | leida_W | -534 | 1 | pot0W_g | 72 | - | pot1W_f | 155
Corriente | pedida | -532 | - | corriente | leida_W | -533.03 | 1.03 | pot0W_g | 72 | - | pot1W_f | 165
Corriente | pedida | -531 | - | corriente | leida_W | -532 | 1 | pot0W_g | 72 | - | pot1W_f | 176
Corriente | pedida | -530 | - | corriente | leida_W | -530.95 | 0.95 | pot0W_g | 72 | - | pot1W_f | 187
Corriente | pedida | -529 | - | corriente | leida_W | -530 | 1 | pot0W_g | 72 | - | pot1W_f | 197
Corriente | pedida | -528 | - | corriente | leida_W | -528.94 | 0.94 | pot0W_g | 72 | - | pot1W_f | 208
Corriente | pedida | -527 | - | corriente | leida_W | -527.98 | 0.98 | pot0W_g | 72 | - | pot1W_f | 218
Corriente | pedida | -526 | - | corriente | leida_W | -527.02 | 1.02 | pot0W_g | 72 | - | pot1W_f | 228
Corriente | pedida | -525 | - | corriente | leida_W | -525.97 | 0.97 | pot0W_g | 72 | - | pot1W_f | 239
Corriente | pedida | -524 | - | corriente | leida_W | -525 | 1 | pot0W_g | 72 | - | pot1W_f | 249
Corriente | pedida | -523 | - | corriente | leida_W | -523.92 | 0.92 | pot0W_g | 73 | - | pot1W_f | 154
Corriente | pedida | -522 | - | corriente | leida_W | -522.89 | 0.89 | pot0W_g | 73 | - | pot1W_f | 165
Corriente | pedida | -521 | - | corriente | leida_W | -521.92 | 0.92 | pot0W_g | 73 | - | pot1W_f | 175
Corriente | pedida | -520 | - | corriente | leida_W | -520.87 | 0.87 | pot0W_g | 73 | - | pot1W_f | 186
Corriente | pedida | -519 | - | corriente | leida_W | -519.89 | 0.89 | pot0W_g | 73 | - | pot1W_f | 196
Corriente | pedida | -518 | - | corriente | leida_W | -518.97 | 0.97 | pot0W_g | 73 | - | pot1W_f | 206
Corriente | pedida | -517 | - | corriente | leida_W | -517.92 | 0.92 | pot0W_g | 73 | - | pot1W_f | 217
Corriente | pedida | -516 | - | corriente | leida_W | -516.94 | 0.94 | pot0W_g | 73 | - | pot1W_f | 227
Corriente | pedida | -515 | - | corriente | leida_W | -515.95 | 0.95 | pot0W_g | 73 | - | pot1W_f | 237
Corriente | pedida | -514 | - | corriente | leida_W | -514.91 | 0.91 | pot0W_g | 73 | - | pot1W_f | 248
Corriente | pedida | -513 | - | corriente | leida_W | -513.97 | 0.97 | pot0W_g | 74 | - | pot1W_f | 151
Corriente | pedida | -512 | - | corriente | leida_W | -512.92 | 0.92 | pot0W_g | 74 | - | pot1W_f | 162
Corriente | pedida | -511 | - | corriente | leida_W | -511.94 | 0.94 | pot0W_g | 74 | - | pot1W_f | 172
Corriente | pedida | -510 | - | corriente | leida_W | -510.91 | 0.91 | pot0W_g | 74 | - | pot1W_f | 183
Corriente | pedida | -509 | - | corriente | leida_W | -509.97 | 0.97 | pot0W_g | 74 | - | pot1W_f | 193
Corriente | pedida | -508 | - | corriente | leida_W | -508.91 | 0.91 | pot0W_g | 74 | - | pot1W_f | 204
Corriente | pedida | -507 | - | corriente | leida_W | -507.94 | 0.94 | pot0W_g | 74 | - | pot1W_f | 214
Corriente | pedida | -506 | - | corriente | leida_W | -506.98 | 0.98 | pot0W_g | 74 | - | pot1W_f | 224
Corriente | pedida | -505 | - | corriente | leida_W | -505.92 | 0.92 | pot0W_g | 74 | - | pot1W_f | 235
Corriente | pedida | -504 | - | corriente | leida_W | -504.87 | 0.87 | pot0W_g | 74 | - | pot1W_f | 246
Corriente | pedida | -503 | - | corriente | leida_W | -503.86 | 0.86 | pot0W_g | 75 | - | pot1W_f | 152
Corriente | pedida | -502 | - | corriente | leida_W | -502.91 | 0.91 | pot0W_g | 75 | - | pot1W_f | 162
Corriente | pedida | -501 | - | corriente | leida_W | -501.87 | 0.87 | pot0W_g | 75 | - | pot1W_f | 173
Corriente | pedida | -500 | - | corriente | leida_W | -500.91 | 0.91 | pot0W_g | 75 | - | pot1W_f | 183
Corriente | pedida | -499 | - | corriente | leida_W | -499.95 | 0.95 | pot0W_g | 75 | - | pot1W_f | 193
Corriente | pedida | -498 | - | corriente | leida_W | -498.89 | 0.89 | pot0W_g | 75 | - | pot1W_f | 204
Corriente | pedida | -497 | - | corriente | leida_W | -497.95 | 0.95 | pot0W_g | 75 | - | pot1W_f | 214
Corriente | pedida | -496 | - | corriente | leida_W | -496.91 | 0.91 | pot0W_g | 75 | - | pot1W_f | 225
Corriente | pedida | -495 | - | corriente | leida_W | -495.92 | 0.92 | pot0W_g | 75 | - | pot1W_f | 235
Corriente | pedida | -494 | - | corriente | leida_W | -494.86 | 0.86 | pot0W_g | 75 | - | pot1W_f | 246
Corriente | pedida | -493 | - | corriente | leida_W | -493.91 | 0.91 | pot0W_g | 76 | - | pot1W_f | 151
Corriente | pedida | -492 | - | corriente | leida_W | -492.94 | 0.94 | pot0W_g | 76 | - | pot1W_f | 161
Corriente | pedida | -491 | - | corriente | leida_W | -492 | 1 | pot0W_g | 76 | - | pot1W_f | 171
Corriente | pedida | -490 | - | corriente | leida_W | -490.95 | 0.95 | pot0W_g | 76 | - | pot1W_f | 182
Corriente | pedida | -489 | - | corriente | leida_W | -489.98 | 0.98 | pot0W_g | 76 | - | pot1W_f | 192
Corriente | pedida | -488 | - | corriente | leida_W | -488.94 | 0.94 | pot0W_g | 76 | - | pot1W_f | 203
Corriente | pedida | -487 | - | corriente | leida_W | -487.87 | 0.87 | pot0W_g | 76 | - | pot1W_f | 214
Corriente | pedida | -486 | - | corriente | leida_W | -486.91 | 0.91 | pot0W_g | 76 | - | pot1W_f | 224
Corriente | pedida | -485 | - | corriente | leida_W | -485.94 | 0.94 | pot0W_g | 76 | - | pot1W_f | 234
Corriente | pedida | -484 | - | corriente | leida_W | -484.91 | 0.91 | pot0W_g | 76 | - | pot1W_f | 245
Corriente | pedida | -483 | - | corriente | leida_W | -483.91 | 0.91 | pot0W_g | 77 | - | pot1W_f | 148
Corriente | pedida | -482 | - | corriente | leida_W | -482.91 | 0.91 | pot0W_g | 77 | - | pot1W_f | 158
Corriente | pedida | -481 | - | corriente | leida_W | -481.86 | 0.86 | pot0W_g | 77 | - | pot1W_f | 169
Corriente | pedida | -480 | - | corriente | leida_W | -480.91 | 0.91 | pot0W_g | 77 | - | pot1W_f | 179
Corriente | pedida | -479 | - | corriente | leida_W | -479.98 | 0.98 | pot0W_g | 77 | - | pot1W_f | 189
Corriente | pedida | -478 | - | corriente | leida_W | -479.02 | 1.02 | pot0W_g | 77 | - | pot1W_f | 199
Corriente | pedida | -477 | - | corriente | leida_W | -477.95 | 0.95 | pot0W_g | 77 | - | pot1W_f | 210
Corriente | pedida | -476 | - | corriente | leida_W | -476.91 | 0.91 | pot0W_g | 77 | - | pot1W_f | 221
Corriente | pedida | -475 | - | corriente | leida_W | -475.95 | 0.95 | pot0W_g | 77 | - | pot1W_f | 231
Corriente | pedida | -474 | - | corriente | leida_W | -474.98 | 0.98 | pot0W_g | 77 | - | pot1W_f | 241
Corriente | pedida | -473 | - | corriente | leida_W | -473.89 | 0.89 | pot0W_g | 78 | - | pot1W_f | 148
Corriente | pedida | -472 | - | corriente | leida_W | -472.91 | 0.91 | pot0W_g | 78 | - | pot1W_f | 158
Corriente | pedida | -471 | - | corriente | leida_W | -471.94 | 0.94 | pot0W_g | 78 | - | pot1W_f | 168
Corriente | pedida | -470 | - | corriente | leida_W | -470.97 | 0.97 | pot0W_g | 78 | - | pot1W_f | 178
Corriente | pedida | -469 | - | corriente | leida_W | -469.94 | 0.94 | pot0W_g | 78 | - | pot1W_f | 189
Corriente | pedida | -468 | - | corriente | leida_W | -469.09 | 1.09 | pot0W_g | 78 | - | pot1W_f | 198
Corriente | pedida | -467 | - | corriente | leida_W | -468.03 | 1.03 | pot0W_g | 78 | - | pot1W_f | 209
Corriente | pedida | -466 | - | corriente | leida_W | -467.08 | 1.08 | pot0W_g | 78 | - | pot1W_f | 219
Corriente | pedida | -465 | - | corriente | leida_W | -466.11 | 1.11 | pot0W_g | 78 | - | pot1W_f | 229
Corriente | pedida | -464 | - | corriente | leida_W | -465.05 | 1.05 | pot0W_g | 78 | - | pot1W_f | 240
Corriente | pedida | -463 | - | corriente | leida_W | -464.06 | 1.06 | pot0W_g | 79 | - | pot1W_f | 146
Corriente | pedida | -462 | - | corriente | leida_W | -463.11 | 1.11 | pot0W_g | 79 | - | pot1W_f | 156
Corriente | pedida | -461 | - | corriente | leida_W | -462.14 | 1.14 | pot0W_g | 79 | - | pot1W_f | 166
Corriente | pedida | -460 | - | corriente | leida_W | -461.08 | 1.08 | pot0W_g | 79 | - | pot1W_f | 177
Corriente | pedida | -459 | - | corriente | leida_W | -460.05 | 1.05 | pot0W_g | 79 | - | pot1W_f | 188
Corriente | pedida | -458 | - | corriente | leida_W | -459.09 | 1.09 | pot0W_g | 79 | - | pot1W_f | 198
Corriente | pedida | -457 | - | corriente | leida_W | -458.11 | 1.11 | pot0W_g | 79 | - | pot1W_f | 208
Corriente | pedida | -456 | - | corriente | leida_W | -457.06 | 1.06 | pot0W_g | 79 | - | pot1W_f | 219
Corriente | pedida | -455 | - | corriente | leida_W | -456.12 | 1.12 | pot0W_g | 79 | - | pot1W_f | 229
Corriente | pedida | -454 | - | corriente | leida_W | -455.17 | 1.17 | pot0W_g | 79 | - | pot1W_f | 239
Corriente | pedida | -453 | - | corriente | leida_W | -454.17 | 1.17 | pot0W_g | 80 | - | pot1W_f | 137
Corriente | pedida | -452 | - | corriente | leida_W | -453.09 | 1.09 | pot0W_g | 80 | - | pot1W_f | 148
Corriente | pedida | -451 | - | corriente | leida_W | -452.12 | 1.12 | pot0W_g | 80 | - | pot1W_f | 158
Corriente | pedida | -450 | - | corriente | leida_W | -451.17 | 1.17 | pot0W_g | 80 | - | pot1W_f | 168
Corriente | pedida | -449 | - | corriente | leida_W | -450.11 | 1.11 | pot0W_g | 80 | - | pot1W_f | 179
Corriente | pedida | -448 | - | corriente | leida_W | -449.19 | 1.19 | pot0W_g | 80 | - | pot1W_f | 189
Corriente | pedida | -447 | - | corriente | leida_W | -448.22 | 1.22 | pot0W_g | 80 | - | pot1W_f | 199
Corriente | pedida | -446 | - | corriente | leida_W | -447.28 | 1.28 | pot0W_g | 80 | - | pot1W_f | 209
Corriente | pedida | -445 | - | corriente | leida_W | -446.23 | 1.23 | pot0W_g | 80 | - | pot1W_f | 220
Corriente | pedida | -444 | - | corriente | leida_W | -445.28 | 1.28 | pot0W_g | 80 | - | pot1W_f | 230
Corriente | pedida | -443 | - | corriente | leida_W | -444.3 | 1.3 | pot0W_g | 80 | - | pot1W_f | 240
Corriente | pedida | -442 | - | corriente | leida_W | -443.22 | 1.22 | pot0W_g | 81 | - | pot1W_f | 148
Corriente | pedida | -441 | - | corriente | leida_W | -442.27 | 1.27 | pot0W_g | 81 | - | pot1W_f | 158
Corriente | pedida | -440 | - | corriente | leida_W | -441.33 | 1.33 | pot0W_g | 81 | - | pot1W_f | 168
Corriente | pedida | -439 | - | corriente | leida_W | -440.27 | 1.27 | pot0W_g | 81 | - | pot1W_f | 179
Corriente | pedida | -438 | - | corriente | leida_W | -439.33 | 1.33 | pot0W_g | 81 | - | pot1W_f | 189
Corriente | pedida | -437 | - | corriente | leida_W | -438.25 | 1.25 | pot0W_g | 81 | - | pot1W_f | 200
Corriente | pedida | -436 | - | corriente | leida_W | -437.28 | 1.28 | pot0W_g | 81 | - | pot1W_f | 210
Corriente | pedida | -435 | - | corriente | leida_W | -436.36 | 1.36 | pot0W_g | 81 | - | pot1W_f | 220
Corriente | pedida | -434 | - | corriente | leida_W | -435.37 | 1.37 | pot0W_g | 81 | - | pot1W_f | 230
Corriente | pedida | -433 | - | corriente | leida_W | -434.31 | 1.31 | pot0W_g | 81 | - | pot1W_f | 241
Corriente | pedida | -432 | - | corriente | leida_W | -433.37 | 1.37 | pot0W_g | 82 | - | pot1W_f | 147
Corriente | pedida | -431 | - | corriente | leida_W | -432.41 | 1.41 | pot0W_g | 82 | - | pot1W_f | 157
Corriente | pedida | -430 | - | corriente | leida_W | -431.34 | 1.34 | pot0W_g | 82 | - | pot1W_f | 168
Corriente | pedida | -429 | - | corriente | leida_W | -430.39 | 1.39 | pot0W_g | 82 | - | pot1W_f | 178
Corriente | pedida | -428 | - | corriente | leida_W | -429.37 | 1.37 | pot0W_g | 82 | - | pot1W_f | 189
Corriente | pedida | -427 | - | corriente | leida_W | -428.39 | 1.39 | pot0W_g | 82 | - | pot1W_f | 199
Corriente | pedida | -426 | - | corriente | leida_W | -427.45 | 1.45 | pot0W_g | 82 | - | pot1W_f | 209
Corriente | pedida | -425 | - | corriente | leida_W | -426.41 | 1.41 | pot0W_g | 82 | - | pot1W_f | 220
Corriente | pedida | -424 | - | corriente | leida_W | -425.44 | 1.44 | pot0W_g | 82 | - | pot1W_f | 230
Corriente | pedida | -423 | - | corriente | leida_W | -424.36 | 1.36 | pot0W_g | 82 | - | pot1W_f | 241
Corriente | pedida | -422 | - | corriente | leida_W | -423.34 | 1.34 | pot0W_g | 83 | - | pot1W_f | 150
Corriente | pedida | -421 | - | corriente | leida_W | -422.39 | 1.39 | pot0W_g | 83 | - | pot1W_f | 160
Corriente | pedida | -420 | - | corriente | leida_W | -421.41 | 1.41 | pot0W_g | 83 | - | pot1W_f | 170
Corriente | pedida | -419 | - | corriente | leida_W | -420.47 | 1.47 | pot0W_g | 83 | - | pot1W_f | 180
Corriente | pedida | -418 | - | corriente | leida_W | -419.45 | 1.45 | pot0W_g | 83 | - | pot1W_f | 191
Corriente | pedida | -417 | - | corriente | leida_W | -418.48 | 1.48 | pot0W_g | 83 | - | pot1W_f | 201
Corriente | pedida | -416 | - | corriente | leida_W | -417.52 | 1.52 | pot0W_g | 83 | - | pot1W_f | 211
Corriente | pedida | -415 | - | corriente | leida_W | -416.48 | 1.48 | pot0W_g | 83 | - | pot1W_f | 222
Corriente | pedida | -414 | - | corriente | leida_W | -415.5 | 1.5 | pot0W_g | 83 | - | pot1W_f | 232
Corriente | pedida | -413 | - | corriente | leida_W | -414.53 | 1.53 | pot0W_g | 83 | - | pot1W_f | 242
Corriente | pedida | -412 | - | corriente | leida_W | -413.45 | 1.45 | pot0W_g | 84 | - | pot1W_f | 151
Corriente | pedida | -411 | - | corriente | leida_W | -412.5 | 1.5 | pot0W_g | 84 | - | pot1W_f | 161
Corriente | pedida | -410 | - | corriente | leida_W | -411.55 | 1.55 | pot0W_g | 84 | - | pot1W_f | 171
Corriente | pedida | -409 | - | corriente | leida_W | -410.61 | 1.61 | pot0W_g | 84 | - | pot1W_f | 181
Corriente | pedida | -408 | - | corriente | leida_W | -409.55 | 1.55 | pot0W_g | 84 | - | pot1W_f | 192
Corriente | pedida | -407 | - | corriente | leida_W | -408.52 | 1.52 | pot0W_g | 84 | - | pot1W_f | 203
Corriente | pedida | -406 | - | corriente | leida_W | -407.44 | 1.44 | pot0W_g | 84 | - | pot1W_f | 214
Corriente | pedida | -405 | - | corriente | leida_W | -406.47 | 1.47 | pot0W_g | 84 | - | pot1W_f | 224
Corriente | pedida | -404 | - | corriente | leida_W | -405.41 | 1.41 | pot0W_g | 84 | - | pot1W_f | 235
Corriente | pedida | -403 | - | corriente | leida_W | -404.47 | 1.47 | pot0W_g | 84 | - | pot1W_f | 245
Corriente | pedida | -402 | - | corriente | leida_W | -403.34 | 1.34 | pot0W_g | 85 | - | pot1W_f | 152
Corriente | pedida | -401 | - | corriente | leida_W | -402.39 | 1.39 | pot0W_g | 85 | - | pot1W_f | 162
Corriente | pedida | -400 | - | corriente | leida_W | -401.44 | 1.44 | pot0W_g | 85 | - | pot1W_f | 172
Corriente | pedida | -399 | - | corriente | leida_W | -400.39 | 1.39 | pot0W_g | 85 | - | pot1W_f | 183
Corriente | pedida | -398 | - | corriente | leida_W | -399.44 | 1.44 | pot0W_g | 85 | - | pot1W_f | 193
Corriente | pedida | -397 | - | corriente | leida_W | -398.47 | 1.47 | pot0W_g | 85 | - | pot1W_f | 203
Corriente | pedida | -396 | - | corriente | leida_W | -397.42 | 1.42 | pot0W_g | 85 | - | pot1W_f | 214
Corriente | pedida | -395 | - | corriente | leida_W | -396.45 | 1.45 | pot0W_g | 85 | - | pot1W_f | 224
Corriente | pedida | -394 | - | corriente | leida_W | -395.41 | 1.41 | pot0W_g | 85 | - | pot1W_f | 235
Corriente | pedida | -393 | - | corriente | leida_W | -394.42 | 1.42 | pot0W_g | 85 | - | pot1W_f | 245
Corriente | pedida | -392 | - | corriente | leida_W | -393.3 | 1.3 | pot0W_g | 86 | - | pot1W_f | 155
Corriente | pedida | -391 | - | corriente | leida_W | -392.34 | 1.34 | pot0W_g | 86 | - | pot1W_f | 165
Corriente | pedida | -390 | - | corriente | leida_W | -391.39 | 1.39 | pot0W_g | 86 | - | pot1W_f | 175
Corriente | pedida | -389 | - | corriente | leida_W | -390.36 | 1.36 | pot0W_g | 86 | - | pot1W_f | 186
Corriente | pedida | -388 | - | corriente | leida_W | -389.31 | 1.31 | pot0W_g | 86 | - | pot1W_f | 197
Corriente | pedida | -387 | - | corriente | leida_W | -388.34 | 1.34 | pot0W_g | 86 | - | pot1W_f | 207
Corriente | pedida | -386 | - | corriente | leida_W | -387.27 | 1.27 | pot0W_g | 86 | - | pot1W_f | 218
Corriente | pedida | -385 | - | corriente | leida_W | -386.31 | 1.31 | pot0W_g | 86 | - | pot1W_f | 228
Corriente | pedida | -384 | - | corriente | leida_W | -385.36 | 1.36 | pot0W_g | 86 | - | pot1W_f | 238
Corriente | pedida | -383 | - | corriente | leida_W | -384.3 | 1.3 | pot0W_g | 86 | - | pot1W_f | 249
Corriente | pedida | -382 | - | corriente | leida_W | -383.28 | 1.28 | pot0W_g | 87 | - | pot1W_f | 158
Corriente | pedida | -381 | - | corriente | leida_W | -382.31 | 1.31 | pot0W_g | 87 | - | pot1W_f | 168
Corriente | pedida | -380 | - | corriente | leida_W | -381.25 | 1.25 | pot0W_g | 87 | - | pot1W_f | 179
Corriente | pedida | -379 | - | corriente | leida_W | -380.25 | 1.25 | pot0W_g | 87 | - | pot1W_f | 190
Corriente | pedida | -378 | - | corriente | leida_W | -379.28 | 1.28 | pot0W_g | 87 | - | pot1W_f | 200
Corriente | pedida | -377 | - | corriente | leida_W | -378.25 | 1.25 | pot0W_g | 87 | - | pot1W_f | 211
Corriente | pedida | -376 | - | corriente | leida_W | -377.25 | 1.25 | pot0W_g | 87 | - | pot1W_f | 221
Corriente | pedida | -375 | - | corriente | leida_W | -376.2 | 1.2 | pot0W_g | 87 | - | pot1W_f | 232
Corriente | pedida | -374 | - | corriente | leida_W | -375.22 | 1.22 | pot0W_g | 87 | - | pot1W_f | 242
Corriente | pedida | -373 | - | corriente | leida_W | -374.25 | 1.25 | pot0W_g | 88 | - | pot1W_f | 152
Corriente | pedida | -372 | - | corriente | leida_W | -373.28 | 1.28 | pot0W_g | 88 | - | pot1W_f | 162
Corriente | pedida | -371 | - | corriente | leida_W | -372.23 | 1.23 | pot0W_g | 88 | - | pot1W_f | 173
Corriente | pedida | -370 | - | corriente | leida_W | -371.3 | 1.3 | pot0W_g | 88 | - | pot1W_f | 183
Corriente | pedida | -369 | - | corriente | leida_W | -370.22 | 1.22 | pot0W_g | 88 | - | pot1W_f | 194
Corriente | pedida | -368 | - | corriente | leida_W | -369.27 | 1.27 | pot0W_g | 88 | - | pot1W_f | 204
Corriente | pedida | -367 | - | corriente | leida_W | -368.23 | 1.23 | pot0W_g | 88 | - | pot1W_f | 215
Corriente | pedida | -366 | - | corriente | leida_W | -367.27 | 1.27 | pot0W_g | 88 | - | pot1W_f | 225
Corriente | pedida | -365 | - | corriente | leida_W | -366.3 | 1.3 | pot0W_g | 88 | - | pot1W_f | 235
Corriente | pedida | -364 | - | corriente | leida_W | -365.25 | 1.25 | pot0W_g | 88 | - | pot1W_f | 246
Corriente | pedida | -363 | - | corriente | leida_W | -364.23 | 1.23 | pot0W_g | 89 | - | pot1W_f | 156
Corriente | pedida | -362 | - | corriente | leida_W | -363.27 | 1.27 | pot0W_g | 89 | - | pot1W_f | 166
Corriente | pedida | -361 | - | corriente | leida_W | -362.23 | 1.23 | pot0W_g | 89 | - | pot1W_f | 177
Corriente | pedida | -360 | - | corriente | leida_W | -361.27 | 1.27 | pot0W_g | 89 | - | pot1W_f | 187
Corriente | pedida | -359 | - | corriente | leida_W | -360.2 | 1.2 | pot0W_g | 89 | - | pot1W_f | 198
Corriente | pedida | -358 | - | corriente | leida_W | -359.27 | 1.27 | pot0W_g | 89 | - | pot1W_f | 208
Corriente | pedida | -357 | - | corriente | leida_W | -358.22 | 1.22 | pot0W_g | 89 | - | pot1W_f | 219
Corriente | pedida | -356 | - | corriente | leida_W | -357.25 | 1.25 | pot0W_g | 89 | - | pot1W_f | 229
Corriente | pedida | -355 | - | corriente | leida_W | -356.2 | 1.2 | pot0W_g | 89 | - | pot1W_f | 240
Corriente | pedida | -354 | - | corriente | leida_W | -355.23 | 1.23 | pot0W_g | 90 | - | pot1W_f | 149
Corriente | pedida | -353 | - | corriente | leida_W | -354.27 | 1.27 | pot0W_g | 90 | - | pot1W_f | 159
Corriente | pedida | -352 | - | corriente | leida_W | -353.17 | 1.17 | pot0W_g | 90 | - | pot1W_f | 170
Corriente | pedida | -351 | - | corriente | leida_W | -352.25 | 1.25 | pot0W_g | 90 | - | pot1W_f | 180
Corriente | pedida | -350 | - | corriente | leida_W | -351.3 | 1.3 | pot0W_g | 90 | - | pot1W_f | 190
Corriente | pedida | -349 | - | corriente | leida_W | -350.25 | 1.25 | pot0W_g | 90 | - | pot1W_f | 201
Corriente | pedida | -348 | - | corriente | leida_W | -349.28 | 1.28 | pot0W_g | 90 | - | pot1W_f | 211
Corriente | pedida | -347 | - | corriente | leida_W | -348.25 | 1.25 | pot0W_g | 90 | - | pot1W_f | 222
Corriente | pedida | -346 | - | corriente | leida_W | -347.28 | 1.28 | pot0W_g | 90 | - | pot1W_f | 232
Corriente | pedida | -345 | - | corriente | leida_W | -346.3 | 1.3 | pot0W_g | 90 | - | pot1W_f | 242
Corriente | pedida | -344 | - | corriente | leida_W | -345.25 | 1.25 | pot0W_g | 91 | - | pot1W_f | 154
Corriente | pedida | -343 | - | corriente | leida_W | -344.3 | 1.3 | pot0W_g | 91 | - | pot1W_f | 164
Corriente | pedida | -342 | - | corriente | leida_W | -343.23 | 1.23 | pot0W_g | 91 | - | pot1W_f | 175
Corriente | pedida | -341 | - | corriente | leida_W | -342.28 | 1.28 | pot0W_g | 91 | - | pot1W_f | 185
Corriente | pedida | -340 | - | corriente | leida_W | -341.22 | 1.22 | pot0W_g | 91 | - | pot1W_f | 196
Corriente | pedida | -339 | - | corriente | leida_W | -340.3 | 1.3 | pot0W_g | 91 | - | pot1W_f | 206
Corriente | pedida | -338 | - | corriente | leida_W | -339.22 | 1.22 | pot0W_g | 91 | - | pot1W_f | 217
Corriente | pedida | -337 | - | corriente | leida_W | -338.25 | 1.25 | pot0W_g | 91 | - | pot1W_f | 227
Corriente | pedida | -336 | - | corriente | leida_W | -337.19 | 1.19 | pot0W_g | 91 | - | pot1W_f | 238
Corriente | pedida | -335 | - | corriente | leida_W | -336.23 | 1.23 | pot0W_g | 91 | - | pot1W_f | 248
Corriente | pedida | -334 | - | corriente | leida_W | -335.19 | 1.19 | pot0W_g | 92 | - | pot1W_f | 159
Corriente | pedida | -333 | - | corriente | leida_W | -334.22 | 1.22 | pot0W_g | 92 | - | pot1W_f | 169
Corriente | pedida | -332 | - | corriente | leida_W | -333.27 | 1.27 | pot0W_g | 92 | - | pot1W_f | 179
Corriente | pedida | -331 | - | corriente | leida_W | -332.23 | 1.23 | pot0W_g | 92 | - | pot1W_f | 190
Corriente | pedida | -330 | - | corriente | leida_W | -331.19 | 1.19 | pot0W_g | 92 | - | pot1W_f | 201
Corriente | pedida | -329 | - | corriente | leida_W | -330.2 | 1.2 | pot0W_g | 92 | - | pot1W_f | 211
Corriente | pedida | -328 | - | corriente | leida_W | -329.17 | 1.17 | pot0W_g | 92 | - | pot1W_f | 222
Corriente | pedida | -327 | - | corriente | leida_W | -328.19 | 1.19 | pot0W_g | 92 | - | pot1W_f | 232
Corriente | pedida | -326 | - | corriente | leida_W | -327.23 | 1.23 | pot0W_g | 92 | - | pot1W_f | 242
Corriente | pedida | -325 | - | corriente | leida_W | -326.17 | 1.17 | pot0W_g | 93 | - | pot1W_f | 151
Corriente | pedida | -324 | - | corriente | leida_W | -325.19 | 1.19 | pot0W_g | 93 | - | pot1W_f | 161
Corriente | pedida | -323 | - | corriente | leida_W | -324.16 | 1.16 | pot0W_g | 93 | - | pot1W_f | 172
Corriente | pedida | -322 | - | corriente | leida_W | -323.2 | 1.2 | pot0W_g | 93 | - | pot1W_f | 182
Corriente | pedida | -321 | - | corriente | leida_W | -322.14 | 1.14 | pot0W_g | 93 | - | pot1W_f | 193
Corriente | pedida | -320 | - | corriente | leida_W | -321.11 | 1.11 | pot0W_g | 93 | - | pot1W_f | 204
Corriente | pedida | -319 | - | corriente | leida_W | -320.14 | 1.14 | pot0W_g | 93 | - | pot1W_f | 214
Corriente | pedida | -318 | - | corriente | leida_W | -319.06 | 1.06 | pot0W_g | 93 | - | pot1W_f | 225
Corriente | pedida | -317 | - | corriente | leida_W | -318.03 | 1.03 | pot0W_g | 93 | - | pot1W_f | 236
Corriente | pedida | -316 | - | corriente | leida_W | -317.05 | 1.05 | pot0W_g | 93 | - | pot1W_f | 246
Corriente | pedida | -315 | - | corriente | leida_W | -315.94 | 0.94 | pot0W_g | 94 | - | pot1W_f | 158
Corriente | pedida | -314 | - | corriente | leida_W | -314.97 | 0.97 | pot0W_g | 94 | - | pot1W_f | 168
Corriente | pedida | -313 | - | corriente | leida_W | -313.94 | 0.94 | pot0W_g | 94 | - | pot1W_f | 179
Corriente | pedida | -312 | - | corriente | leida_W | -312.97 | 0.97 | pot0W_g | 94 | - | pot1W_f | 189
Corriente | pedida | -311 | - | corriente | leida_W | -311.94 | 0.94 | pot0W_g | 94 | - | pot1W_f | 200
Corriente | pedida | -310 | - | corriente | leida_W | -310.97 | 0.97 | pot0W_g | 94 | - | pot1W_f | 210
Corriente | pedida | -309 | - | corriente | leida_W | -310.02 | 1.02 | pot0W_g | 94 | - | pot1W_f | 220
Corriente | pedida | -308 | - | corriente | leida_W | -308.95 | 0.95 | pot0W_g | 94 | - | pot1W_f | 231
Corriente | pedida | -307 | - | corriente | leida_W | -308.02 | 1.02 | pot0W_g | 94 | - | pot1W_f | 241
Corriente | pedida | -306 | - | corriente | leida_W | -306.98 | 0.98 | pot0W_g | 95 | - | pot1W_f | 152
Corriente | pedida | -305 | - | corriente | leida_W | -306.03 | 1.03 | pot0W_g | 95 | - | pot1W_f | 162
Corriente | pedida | -304 | - | corriente | leida_W | -305 | 1 | pot0W_g | 95 | - | pot1W_f | 173
Corriente | pedida | -303 | - | corriente | leida_W | -304.02 | 1.02 | pot0W_g | 95 | - | pot1W_f | 183
Corriente | pedida | -302 | - | corriente | leida_W | -302.97 | 0.97 | pot0W_g | 95 | - | pot1W_f | 194
Corriente | pedida | -301 | - | corriente | leida_W | -301.92 | 0.92 | pot0W_g | 95 | - | pot1W_f | 205
Corriente | pedida | -300 | - | corriente | leida_W | -300.95 | 0.95 | pot0W_g | 95 | - | pot1W_f | 215
Corriente | pedida | -299 | - | corriente | leida_W | -300.02 | 1.02 | pot0W_g | 95 | - | pot1W_f | 225
Corriente | pedida | -298 | - | corriente | leida_W | -298.94 | 0.94 | pot0W_g | 95 | - | pot1W_f | 236
Corriente | pedida | -297 | - | corriente | leida_W | -297.97 | 0.97 | pot0W_g | 95 | - | pot1W_f | 246
Corriente | pedida | -296 | - | corriente | leida_W | -296.97 | 0.97 | pot0W_g | 96 | - | pot1W_f | 142
Corriente | pedida | -295 | - | corriente | leida_W | -296 | 1 | pot0W_g | 96 | - | pot1W_f | 152
Corriente | pedida | -294 | - | corriente | leida_W | -295.03 | 1.03 | pot0W_g | 96 | - | pot1W_f | 162
Corriente | pedida | -293 | - | corriente | leida_W | -293.98 | 0.98 | pot0W_g | 96 | - | pot1W_f | 173
Corriente | pedida | -292 | - | corriente | leida_W | -292.92 | 0.92 | pot0W_g | 96 | - | pot1W_f | 184
Corriente | pedida | -291 | - | corriente | leida_W | -291.97 | 0.97 | pot0W_g | 96 | - | pot1W_f | 194
Corriente | pedida | -290 | - | corriente | leida_W | -290.92 | 0.92 | pot0W_g | 96 | - | pot1W_f | 205
Corriente | pedida | -289 | - | corriente | leida_W | -289.97 | 0.97 | pot0W_g | 96 | - | pot1W_f | 215
Corriente | pedida | -288 | - | corriente | leida_W | -288.91 | 0.91 | pot0W_g | 96 | - | pot1W_f | 226
Corriente | pedida | -287 | - | corriente | leida_W | -287.84 | 0.84 | pot0W_g | 96 | - | pot1W_f | 237
Corriente | pedida | -286 | - | corriente | leida_W | -286.86 | 0.86 | pot0W_g | 96 | - | pot1W_f | 247
Corriente | pedida | -285 | - | corriente | leida_W | -285.89 | 0.89 | pot0W_g | 97 | - | pot1W_f | 159
Corriente | pedida | -284 | - | corriente | leida_W | -284.91 | 0.91 | pot0W_g | 97 | - | pot1W_f | 169
Corriente | pedida | -283 | - | corriente | leida_W | -283.89 | 0.89 | pot0W_g | 97 | - | pot1W_f | 180
Corriente | pedida | -282 | - | corriente | leida_W | -282.94 | 0.94 | pot0W_g | 97 | - | pot1W_f | 190
Corriente | pedida | -281 | - | corriente | leida_W | -281.98 | 0.98 | pot0W_g | 97 | - | pot1W_f | 200
Corriente | pedida | -280 | - | corriente | leida_W | -280.92 | 0.92 | pot0W_g | 97 | - | pot1W_f | 211
Corriente | pedida | -279 | - | corriente | leida_W | -279.87 | 0.87 | pot0W_g | 97 | - | pot1W_f | 222
Corriente | pedida | -278 | - | corriente | leida_W | -278.89 | 0.89 | pot0W_g | 97 | - | pot1W_f | 232
Corriente | pedida | -277 | - | corriente | leida_W | -277.94 | 0.94 | pot0W_g | 97 | - | pot1W_f | 242
Corriente | pedida | -276 | - | corriente | leida_W | -276.84 | 0.84 | pot0W_g | 98 | - | pot1W_f | 154
Corriente | pedida | -275 | - | corriente | leida_W | -276 | 1 | pot0W_g | 98 | - | pot1W_f | 163
Corriente | pedida | -274 | - | corriente | leida_W | -274.95 | 0.95 | pot0W_g | 98 | - | pot1W_f | 174
Corriente | pedida | -273 | - | corriente | leida_W | -273.91 | 0.91 | pot0W_g | 98 | - | pot1W_f | 185
Corriente | pedida | -272 | - | corriente | leida_W | -272.95 | 0.95 | pot0W_g | 98 | - | pot1W_f | 195
Corriente | pedida | -271 | - | corriente | leida_W | -272 | 1 | pot0W_g | 98 | - | pot1W_f | 205
Corriente | pedida | -270 | - | corriente | leida_W | -270.97 | 0.97 | pot0W_g | 98 | - | pot1W_f | 216
Corriente | pedida | -269 | - | corriente | leida_W | -269.97 | 0.97 | pot0W_g | 98 | - | pot1W_f | 226
Corriente | pedida | -268 | - | corriente | leida_W | -268.92 | 0.92 | pot0W_g | 98 | - | pot1W_f | 237
Corriente | pedida | -267 | - | corriente | leida_W | -267.94 | 0.94 | pot0W_g | 98 | - | pot1W_f | 247
Corriente | pedida | -266 | - | corriente | leida_W | -266.95 | 0.95 | pot0W_g | 99 | - | pot1W_f | 160
Corriente | pedida | -265 | - | corriente | leida_W | -265.91 | 0.91 | pot0W_g | 99 | - | pot1W_f | 171
Corriente | pedida | -264 | - | corriente | leida_W | -264.86 | 0.86 | pot0W_g | 99 | - | pot1W_f | 182
Corriente | pedida | -263 | - | corriente | leida_W | -263.91 | 0.91 | pot0W_g | 99 | - | pot1W_f | 192
Corriente | pedida | -262 | - | corriente | leida_W | -262.86 | 0.86 | pot0W_g | 99 | - | pot1W_f | 203
Corriente | pedida | -261 | - | corriente | leida_W | -261.91 | 0.91 | pot0W_g | 99 | - | pot1W_f | 213
Corriente | pedida | -260 | - | corriente | leida_W | -260.83 | 0.83 | pot0W_g | 99 | - | pot1W_f | 224
Corriente | pedida | -259 | - | corriente | leida_W | -259.87 | 0.87 | pot0W_g | 99 | - | pot1W_f | 234
Corriente | pedida | -258 | - | corriente | leida_W | -258.91 | 0.91 | pot0W_g | 99 | - | pot1W_f | 244
Corriente | pedida | -257 | - | corriente | leida_W | -257.84 | 0.84 | pot0W_g | 100 | - | pot1W_f | 157
Corriente | pedida | -256 | - | corriente | leida_W | -256.87 | 0.87 | pot0W_g | 100 | - | pot1W_f | 167
Corriente | pedida | -255 | - | corriente | leida_W | -255.83 | 0.83 | pot0W_g | 100 | - | pot1W_f | 178
Corriente | pedida | -254 | - | corriente | leida_W | -254.91 | 0.91 | pot0W_g | 100 | - | pot1W_f | 188
Corriente | pedida | -253 | - | corriente | leida_W | -253.95 | 0.95 | pot0W_g | 100 | - | pot1W_f | 198
Corriente | pedida | -252 | - | corriente | leida_W | -252.89 | 0.89 | pot0W_g | 100 | - | pot1W_f | 209
Corriente | pedida | -251 | - | corriente | leida_W | -251.94 | 0.94 | pot0W_g | 100 | - | pot1W_f | 219
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
