fablabbcn/smartcitizen-kit-gases-pro-board/test_utils/data/source_A_board_1/source_W_board_1_rand_06.ods

item | Corriente pedida |  | delay |  | corriente leida_W | diff
0 | 10 | -> | 2000 | - | 9.25 | 0.75
1 | -594 | -> | 1104 | - | -594.81 | 0.81
2 | 682 | -> | 1776 | - | 682.94 | -0.94
3 | -125 | -> | 1307 | - | -125.09 | 0.09
4 | -376 | -> | 751 | - | -376.39 | 0.39
5 | 229 | -> | 1105 | - | 229.67 | -0.67
6 | 615 | -> | 886 | - | 615.69 | -0.69
7 | -308 | -> | 1423 | - | -308.09 | 0.09
8 | -1072 | -> | 1264 | - | -1073.72 | 1.72
9 | 702 | -> | 2274 | - | 703.16 | -1.16
10 | -626 | -> | 1828 | - | -627.03 | 1.03
11 | -817 | -> | 691 | - | -817.73 | 0.73
12 | -152 | -> | 1165 | - | -152.28 | 0.28
13 | -16 | -> | 636 | - | -16.44 | 0.44
14 | -264 | -> | 748 | - | -263.91 | -0.09
15 | 1081 | -> | 1845 | - | 1082.41 | -1.41
16 | -857 | -> | 2438 | - | -857.7 | 0.7
17 | 913 | -> | 2270 | - | 914.37 | -1.37
18 | 984 | -> | 571 | - | 985.2 | -1.2
19 | -1344 | -> | 2828 | - | -1346.16 | 2.16
20 | 512 | -> | 2356 | - | 512.34 | -0.34
21 | 1230 | -> | 1218 | - | 1231.78 | -1.78
22 | -695 | -> | 2425 | - | -696.22 | 1.22
23 | 1394 | -> | 2589 | - | 1396.66 | -2.66
24 | -24 | -> | 1918 | - | -23.98 | -0.02
25 | -849 | -> | 1325 | - | -849.64 | 0.64
26 | 1137 | -> | 2486 | - | 1138.31 | -1.31
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
