fablabbcn/smartcitizen-kit-gases-pro-board/test_utils/data/source_A_board_2/source_A_board_2_lin_02.ods

Corriente pedida |  | corriente leida_A | diff
-1400 | - | -1400 | 0 | pot0A_g | 3 | - | pot1A_f | 199
-1399 | - | -1398.95 | -0.05 | pot0A_g | 3 | - | pot1A_f | 210
-1398 | - | -1398 | 0 | pot0A_g | 3 | - | pot1A_f | 220
-1397 | - | -1397.03 | 0.03 | pot0A_g | 3 | - | pot1A_f | 230
-1396 | - | -1395.94 | -0.06 | pot0A_g | 3 | - | pot1A_f | 241
-1395 | - | -1394.95 | -0.05 | pot0A_g | 4 | - | pot1A_f | 82
-1394 | - | -1393.97 | -0.03 | pot0A_g | 4 | - | pot1A_f | 92
-1393 | - | -1393.03 | 0.03 | pot0A_g | 4 | - | pot1A_f | 102
-1392 | - | -1391.97 | -0.03 | pot0A_g | 4 | - | pot1A_f | 113
-1391 | - | -1391.03 | 0.03 | pot0A_g | 4 | - | pot1A_f | 123
-1390 | - | -1389.98 | -0.02 | pot0A_g | 4 | - | pot1A_f | 134
-1389 | - | -1389.02 | 0.02 | pot0A_g | 4 | - | pot1A_f | 144
-1388 | - | -1388.05 | 0.05 | pot0A_g | 4 | - | pot1A_f | 154
-1387 | - | -1387 | 0 | pot0A_g | 4 | - | pot1A_f | 165
-1386 | - | -1386.03 | 0.03 | pot0A_g | 4 | - | pot1A_f | 175
-1385 | - | -1385 | 0 | pot0A_g | 4 | - | pot1A_f | 186
-1384 | - | -1383.95 | -0.05 | pot0A_g | 4 | - | pot1A_f | 197
-1383 | - | -1383 | 0 | pot0A_g | 4 | - | pot1A_f | 207
-1382 | - | -1382.05 | 0.05 | pot0A_g | 4 | - | pot1A_f | 217
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
