fablabbcn/smartcitizen-kit-gases-pro-board/test_utils/data/source_A_board_2/source_A_board_2_ran_03.ods

item | Corriente pedida |  | delay |  | corriente leida_A | diff
0 | 394 | -> | 2000 | - | 393.78 | 0.22
1 | 1190 | -> | 1296 | - | 1189.28 | 0.72
2 | -1098 | -> | 2788 | - | -1097.56 | -0.44
3 | -584 | -> | 1014 | - | -584.27 | 0.27
4 | 236 | -> | 1320 | - | 235.52 | 0.48
5 | -316 | -> | 1052 | - | -315.87 | -0.13
6 | 879 | -> | 1695 | - | 878.48 | 0.52
7 | 1094 | -> | 715 | - | 1093.27 | 0.73
8 | 376 | -> | 1218 | - | 376.03 | -0.03
9 | 1012 | -> | 1136 | - | 1011.53 | 0.47
10 | 1165 | -> | 653 | - | 1164.39 | 0.61
11 | -917 | -> | 2582 | - | -916.75 | -0.25
12 | -1233 | -> | 816 | - | -1232.2 | -0.8
13 | -26 | -> | 1707 | - | -26.39 | 0.39
14 | 1122 | -> | 1648 | - | 1121.39 | 0.61
15 | 641 | -> | 981 | - | 640.89 | 0.11
16 | 715 | -> | 574 | - | 714.8 | 0.2
17 | 281 | -> | 934 | - | 281.16 | -0.16
18 | 162 | -> | 619 | - | 162.09 | -0.09
19 | 1185 | -> | 1523 | - | 1184.52 | 0.48
20 | 620 | -> | 1065 | - | 620.03 | -0.03
21 | 1075 | -> | 955 | - | 1074.66 | 0.34
22 | 1119 | -> | 544 | - | 1118.63 | 0.37
23 | 59 | -> | 1560 | - | 59.2 | -0.2
24 | -848 | -> | 1407 | - | -847.55 | -0.45
25 | 71 | -> | 1419 | - | 70.73 | 0.27
26 | 910 | -> | 1339 | - | 909.55 | 0.45
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
