fablabbcn/smartcitizen-kit-gases-pro-board/currentLookUp_Board_0.h

// For board 0 (the first handmade one)
static const uint8_t CURRENT_LOOKUP_A [][2] PROGMEM = {
{243,46},
{243,44},{243,40},{243,37},{243,33},{243,29},{243,26},{243,22},{243,18},{243,15},{243,11},
{243,7},{242,49},{242,47},{242,43},{242,39},{242,36},{242,32},{242,29},{242,25},{242,21},
{242,18},{242,14},{242,10},{242,6},{241,48},{241,46},{241,42},{241,39},{241,35},{241,31},
{241,28},{241,24},{241,20},{241,17},{241,13},{241,10},{240,51},{240,49},{240,46},{240,42},
{240,38},{240,34},{240,31},{240,27},{240,24},{240,20},{240,16},{240,12},{240,9},{239,53},
{239,51},{239,47},{239,44},{239,40},{239,36},{239,33},{239,29},{239,25},{239,22},{239,18},
{239,14},{239,10},{239,7},{238,49},{238,47},{238,43},{238,39},{238,36},{238,32},{238,28},
{238,25},{238,21},{238,17},{238,14},{238,10},{237,51},{237,49},{237,45},{237,42},{237,38},
{237,34},{237,31},{237,27},{237,24},{237,20},{237,16},{237,12},{237,9},{236,51},{236,48},
{236,45},{236,41},{236,38},{236,34},{236,30},{236,26},{236,23},{236,19},{236,16},{236,12},
{236,8},{235,50},{235,47},{235,44},{235,40},{235,36},{235,33},{235,29},{235,25},{235,22},
{235,18},{235,15},{235,11},{235,7},{234,48},{234,46},{234,43},{234,39},{234,35},{234,32},
{234,28},{234,24},{234,21},{234,17},{234,13},{234,9},{233,51},{233,49},{233,45},{233,41},
{233,38},{233,34},{233,30},{233,27},{233,23},{233,20},{233,16},{233,12},{233,9},{232,50},
{232,48},{232,44},{232,40},{232,37},{232,33},{232,29},{232,26},{232,22},{232,19},{232,15},
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
{215,26},{215,22},{215,18},{215,14},{215,10},{215,6},{214,50},{214,47},{214,44},{214,40},
{214,36},{214,32},{214,28},{214,24},{214,20},{214,16},{214,13},{214,9},{213,51},{213,49},
{213,45},{213,41},{213,38},{213,34},{213,30},{213,26},{213,22},{213,18},{213,14},{213,11},
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
};
