fablabbcn/smartcitizen-kit-gases-pro-board/currentLookUp_Board_1.h

// For board 1 (seeed fusion built v0.3 - 04/2018)
static const uint8_t CURRENT_LOOKUP_A [][2] PROGMEM = {
{3,196},
{3,207},{3,217},{3,228},{3,238},{3,249},{4,90},{4,100},{4,111},{4,121},{4,132},
{4,142},{4,153},{4,163},{4,174},{4,184},{4,195},{4,205},{4,216},{4,226},{4,237},
{4,247},{5,90},{5,100},{5,111},{5,121},{5,131},{5,142},{5,153},{5,163},{5,173},
{5,184},{5,194},{5,205},{5,215},{5,226},{5,236},{5,247},{6,92},{6,102},{6,112},
{6,123},{6,134},{6,144},{6,154},{6,165},{6,176},{6,186},{6,196},{6,207},{6,217},
{6,228},{6,238},{6,249},{7,94},{7,105},{7,115},{7,125},{7,136},{7,146},{7,157},
{7,167},{7,178},{7,188},{7,199},{7,209},{7,220},{7,230},{7,241},{8,81},{8,92},
{8,102},{8,113},{8,123},{8,133},{8,144},{8,154},{8,165},{8,175},{8,186},{8,197},
{8,207},{8,217},{8,228},{8,238},{8,249},{9,96},{9,107},{9,117},{9,127},{9,138},
{9,149},{9,159},{9,170},{9,180},{9,191},{9,201},{9,212},{9,222},{9,233},{9,243},
{10,96},{10,106},{10,116},{10,127},{10,138},{10,148},{10,158},{10,169},{10,179},{10,190},
{10,200},{10,211},{10,221},{10,232},{10,242},{11,95},{11,105},{11,115},{11,126},{11,136},
{11,147},{11,157},{11,167},{11,178},{11,188},{11,199},{11,209},{11,220},{11,230},{11,241},
{12,94},{12,104},{12,115},{12,125},{12,136},{12,146},{12,156},{12,167},{12,177},{12,188},
{12,198},{12,209},{12,219},{12,230},{12,240},{13,95},{13,105},{13,116},{13,126},{13,136},
{13,147},{13,157},{13,168},{13,178},{13,189},{13,199},{13,210},{13,220},{13,231},{13,241},
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
{29,113},{29,123},{29,133},{29,144},{29,155},{29,165},{29,175},{29,186},{29,197},{29,207},
{29,218},{29,228},{29,239},{29,249},{30,125},{30,135},{30,146},{30,156},{30,167},{30,177},
{30,188},{30,198},{30,209},{30,219},{30,229},{30,240},{31,116},{31,126},{31,137},{31,147},
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
};
