fablabbcn/smartcitizen-kit-gases-pro-board/currentLookUp_Board_3.h

// For board 3 (seeed fusion built v0.3 - 04/2018)
static const uint8_t CURRENT_LOOKUP_A [][2] PROGMEM = {
{3,195},
{3,205},{3,216},{3,226},{3,237},{3,247},{4,90},{4,100},{4,110},{4,121},{4,131},
{4,142},{4,153},{4,163},{4,174},{4,184},{4,194},{4,204},{4,215},{4,225},{4,236},
{4,246},{5,91},{5,101},{5,111},{5,122},{5,132},{5,143},{5,153},{5,163},{5,174},
{5,185},{5,195},{5,205},{5,216},{5,226},{5,237},{5,247},{6,92},{6,102},{6,113},
{6,123},{6,134},{6,144},{6,154},{6,165},{6,175},{6,186},{6,196},{6,207},{6,217},
{6,227},{6,238},{6,248},{7,96},{7,106},{7,117},{7,127},{7,138},{7,148},{7,159},
{7,169},{7,180},{7,190},{7,200},{7,211},{7,221},{7,232},{7,242},{8,75},{8,85},
{8,95},{8,106},{8,116},{8,126},{8,137},{8,148},{8,158},{8,168},{8,179},{8,189},
{8,200},{8,210},{8,220},{8,231},{8,241},{9,92},{9,102},{9,113},{9,123},{9,134},
{9,144},{9,155},{9,165},{9,176},{9,186},{9,196},{9,207},{9,217},{9,228},{9,238},
{9,249},{10,100},{10,110},{10,121},{10,131},{10,142},{10,152},{10,163},{10,173},{10,184},
{10,194},{10,204},{10,215},{10,225},{10,236},{10,246},{11,101},{11,111},{11,121},{11,132},
{11,142},{11,152},{11,163},{11,173},{11,184},{11,194},{11,205},{11,215},{11,225},{11,236},
{11,246},{12,100},{12,111},{12,121},{12,132},{12,142},{12,153},{12,163},{12,173},{12,184},
{12,194},{12,205},{12,215},{12,225},{12,236},{12,246},{13,102},{13,113},{13,123},{13,133},
{13,144},{13,154},{13,165},{13,175},{13,186},{13,196},{13,206},{13,217},{13,227},{13,238},
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
{28,153},{28,163},{28,173},{28,184},{28,194},{28,205},{28,215},{28,225},{28,236},{28,246},
{29,123},{29,133},{29,144},{29,155},{29,165},{29,175},{29,186},{29,196},{29,207},{29,217},
{29,227},{29,238},{29,248},{30,122},{30,132},{30,143},{30,153},{30,164},{30,174},{30,185},
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
};
